daveho/DIY8bit/Episode0a/README.md

# Episode A: Arduino-based EEPROM programmer

This episode documents a project to create a programmer (hardware, firmware, host utility) for 28C64 and 28C256 EEPROM devices.

Git repo containing the schematics, firmware code, and host utility code: https://github.com/daveho/eeprog
