daveho/DIY8bit/Episode1a/Experiment02b/README.txt

Like Experiment02a, but uses 159 MHz as the main clock frequency,
meaning that the SVGA 800x600 dot clock is 39.75 MHz rather than
40 MHz. This is *almost* within the 0.5% VESA tolerance, and does
in fact work just fine on my IBM monitor.
