daveho/DIY8bit/Episode1a/Experiment02/README.txt

Experiment 2 is to connect the command FIFO to the FPGA,
without actually responding to commands sent by the host.
