daveho/DIY8bit/Episode1a/Experiment00/README.txt

Experiment 0 is just adding a reset input, but not using it.
