daveho/DIY8bit/Episode1a/Experiment01/README.txt

Experiment 1 is to add a reset input to the display
controller.
