daveho/DIY8bit/Episode05/DTypeLatchAsyncSetReset/DTypeLatchAsyncSetReset.pdf

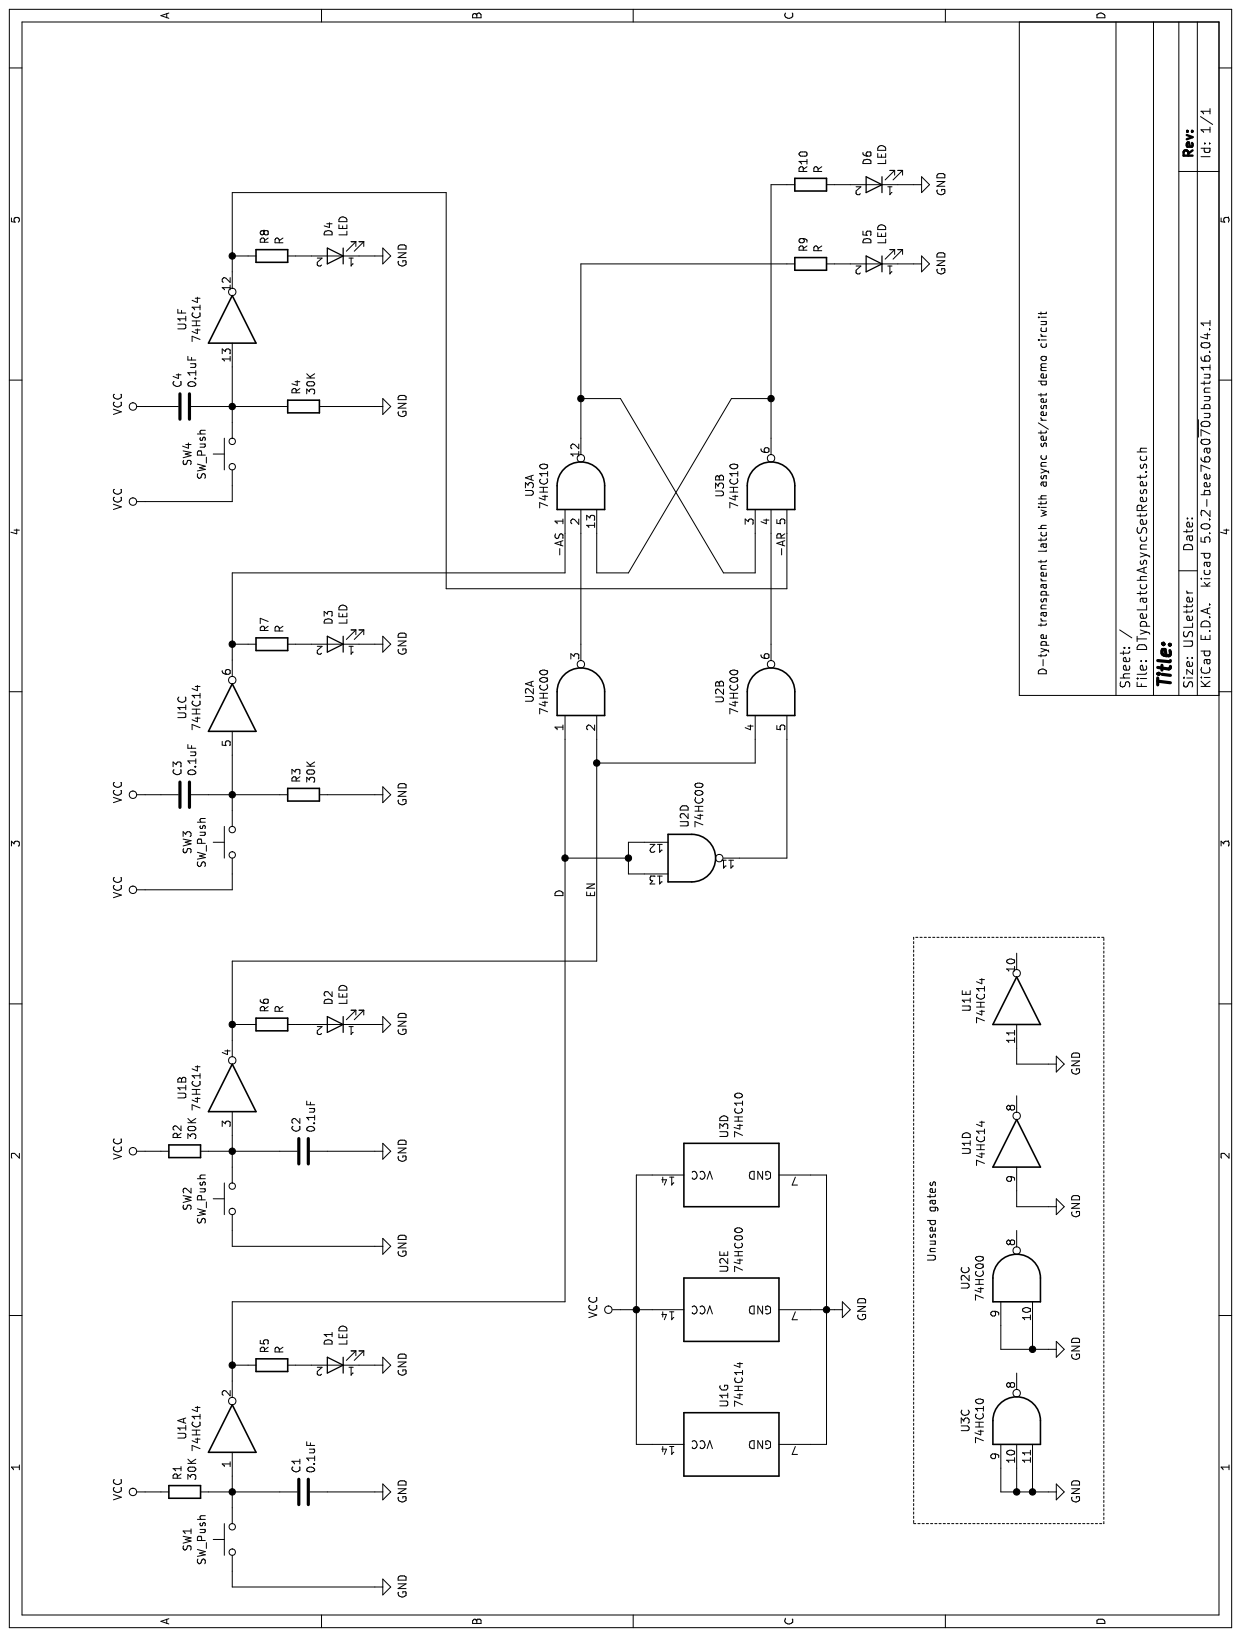
[picture p65: page 1]
