daveho/DIY8bit/Episode05/DTypeLatch/DTypeLatch.pdf

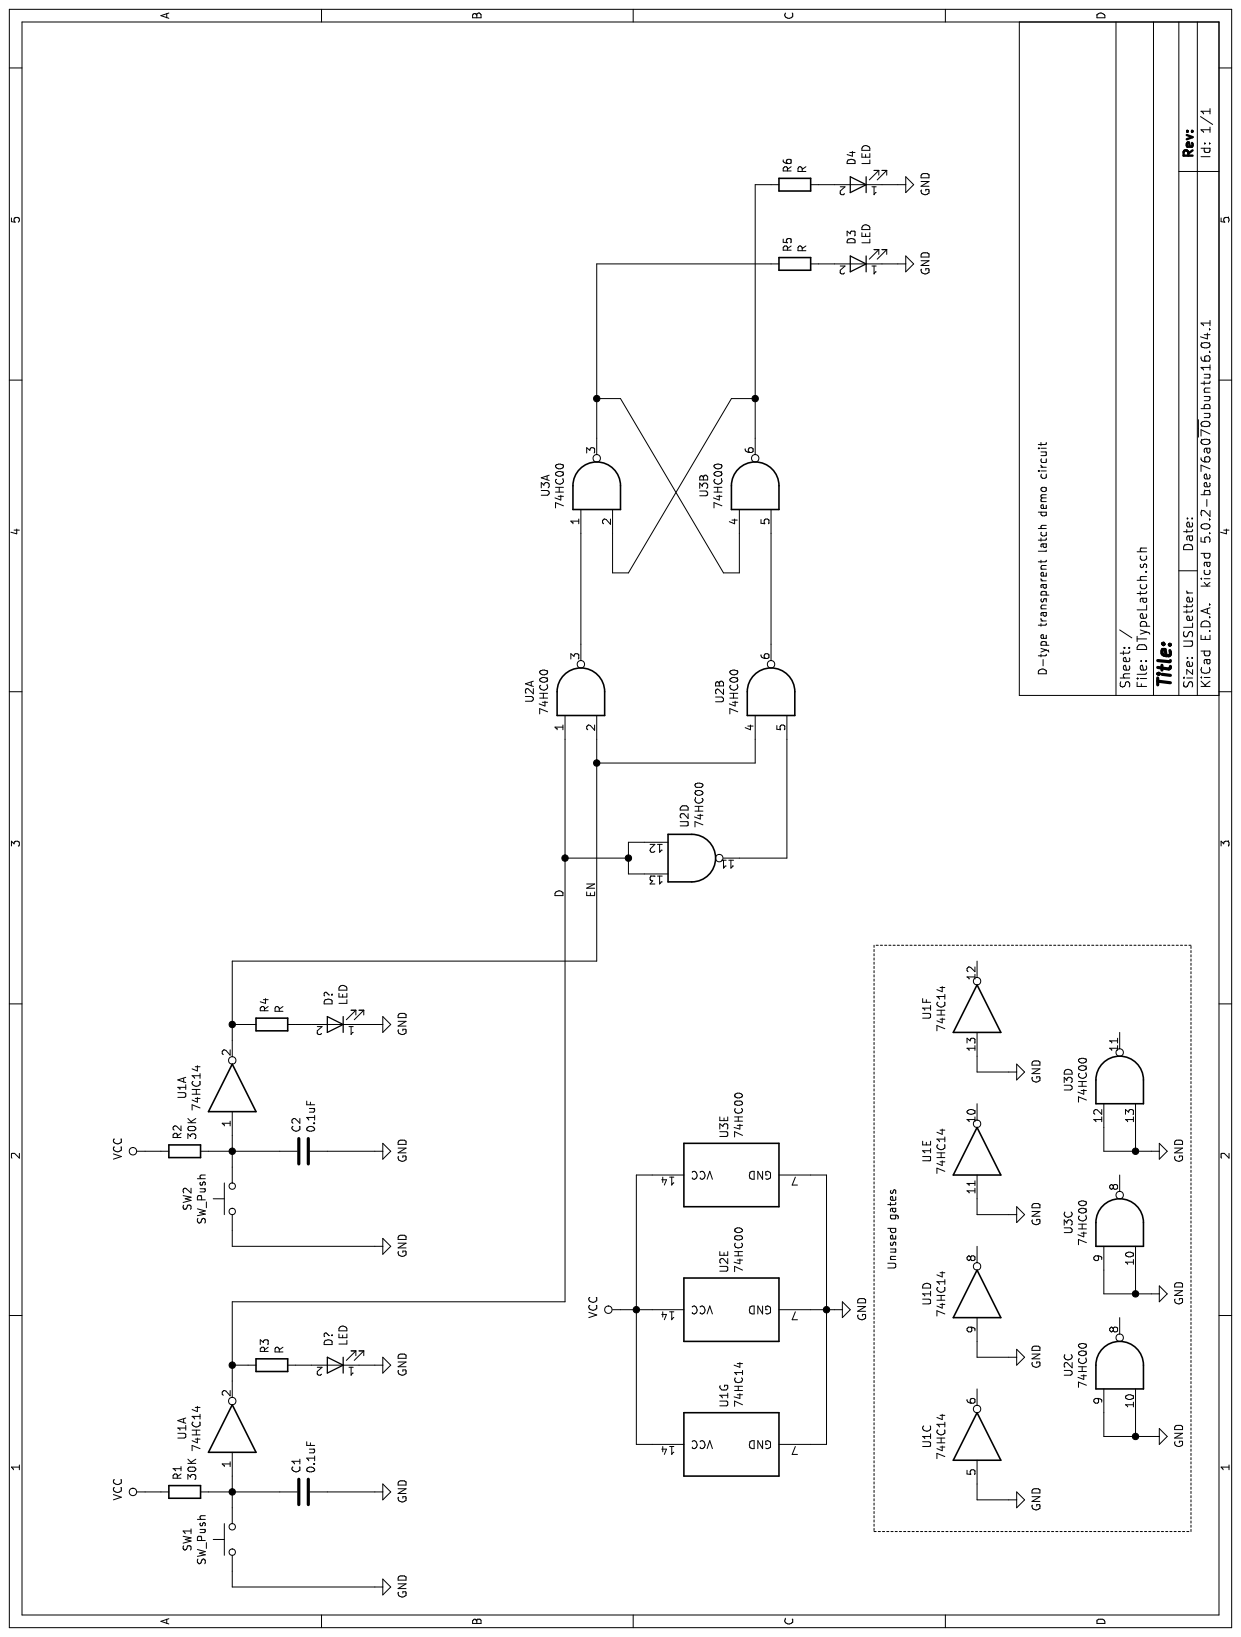
[picture p66: page 1]
