daveho/DIY8bit/Episode05/SRLatch/SRLatch.pdf

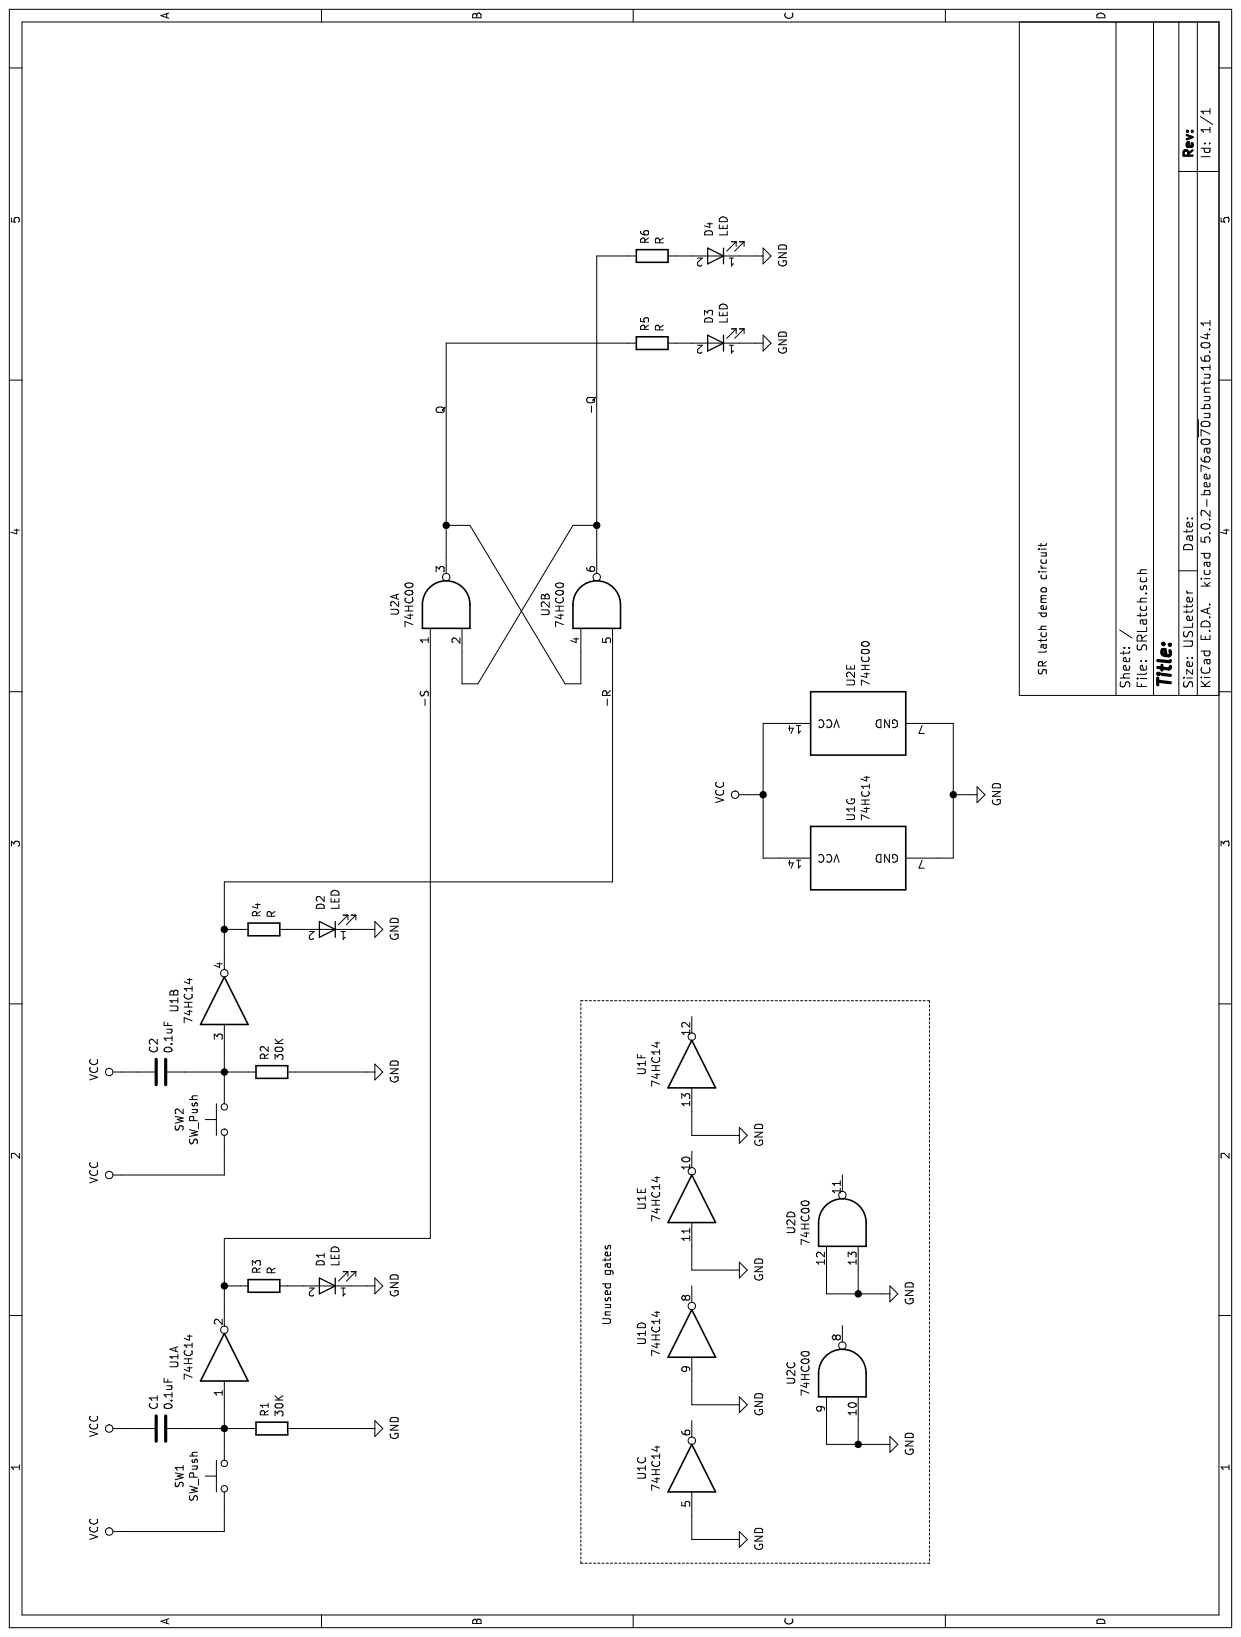
[picture p67: page 1]
