daveho/DIY8bit/Episode05/DTypeEdgeTriggered/DTypeEdgeTriggered.pdf

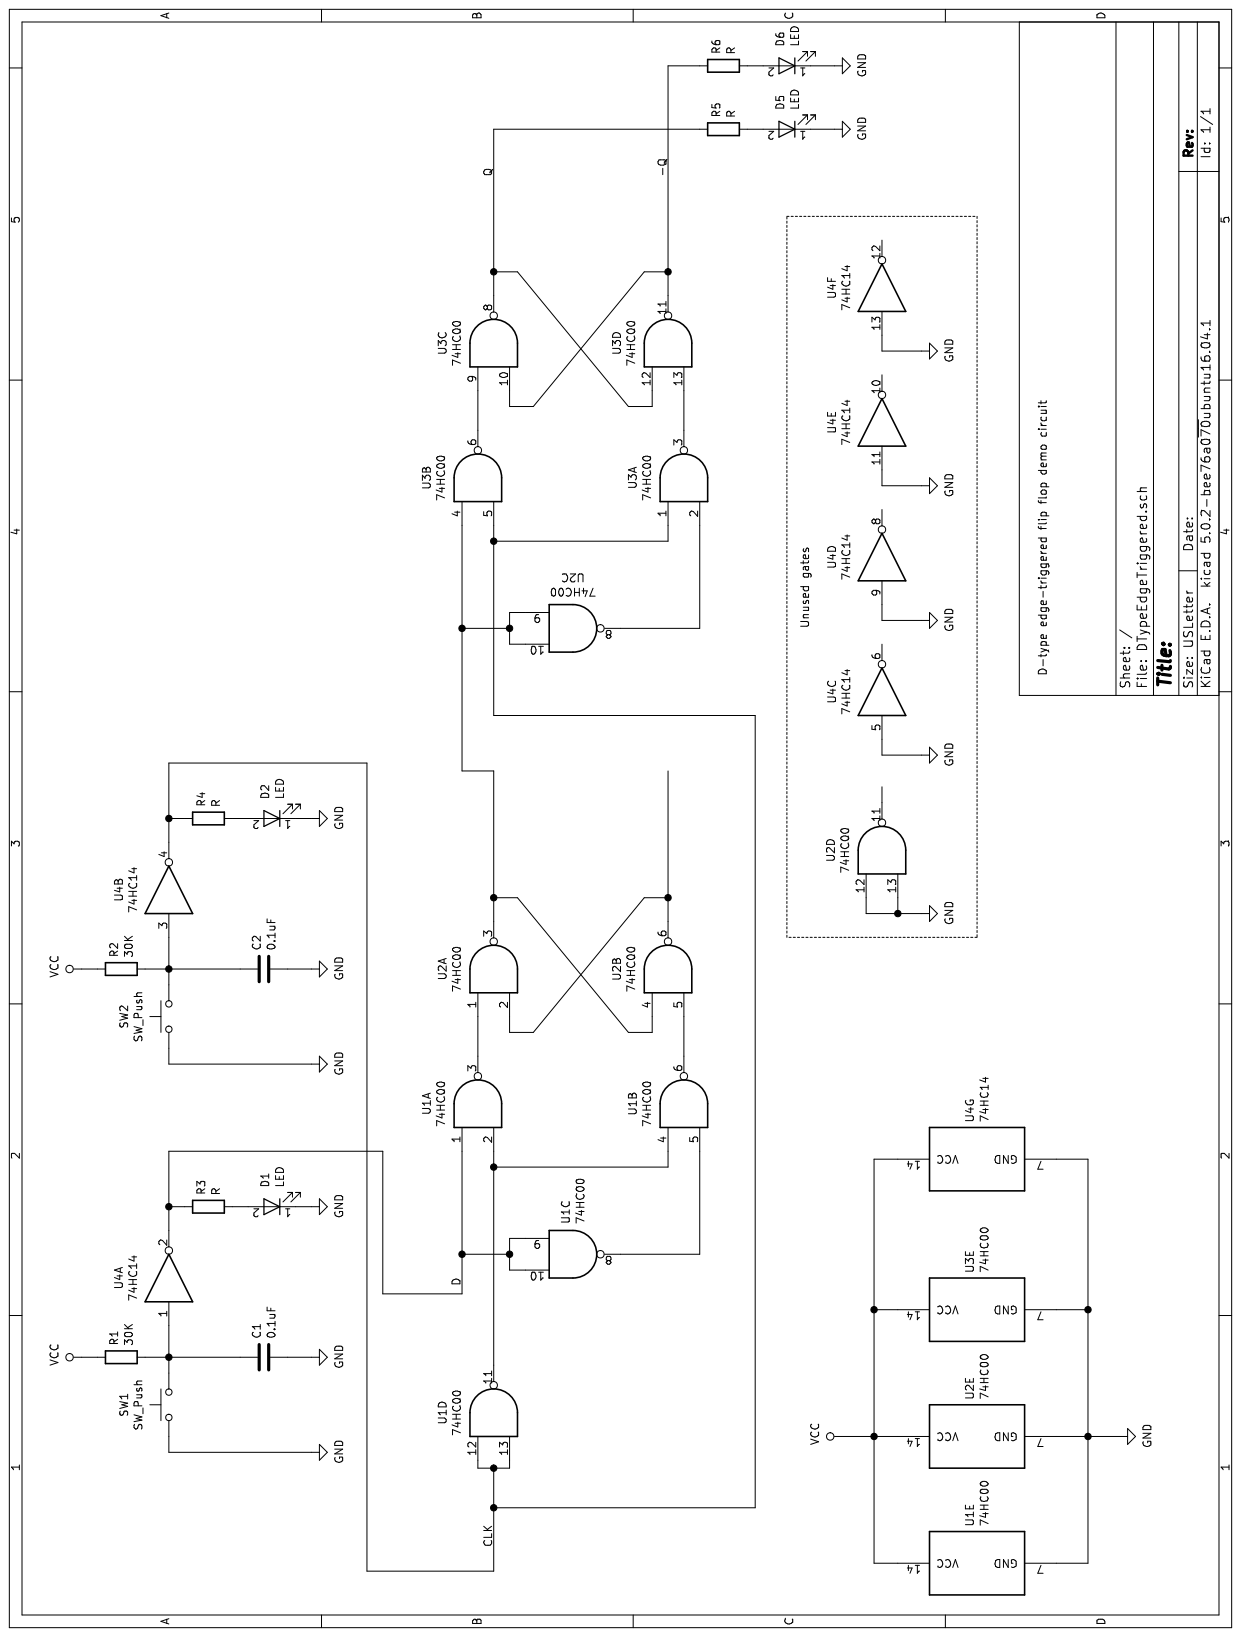
[picture p68: page 1]
