daveho/DIY8bit/GALDisplayController/HW_VGA_old.pdf

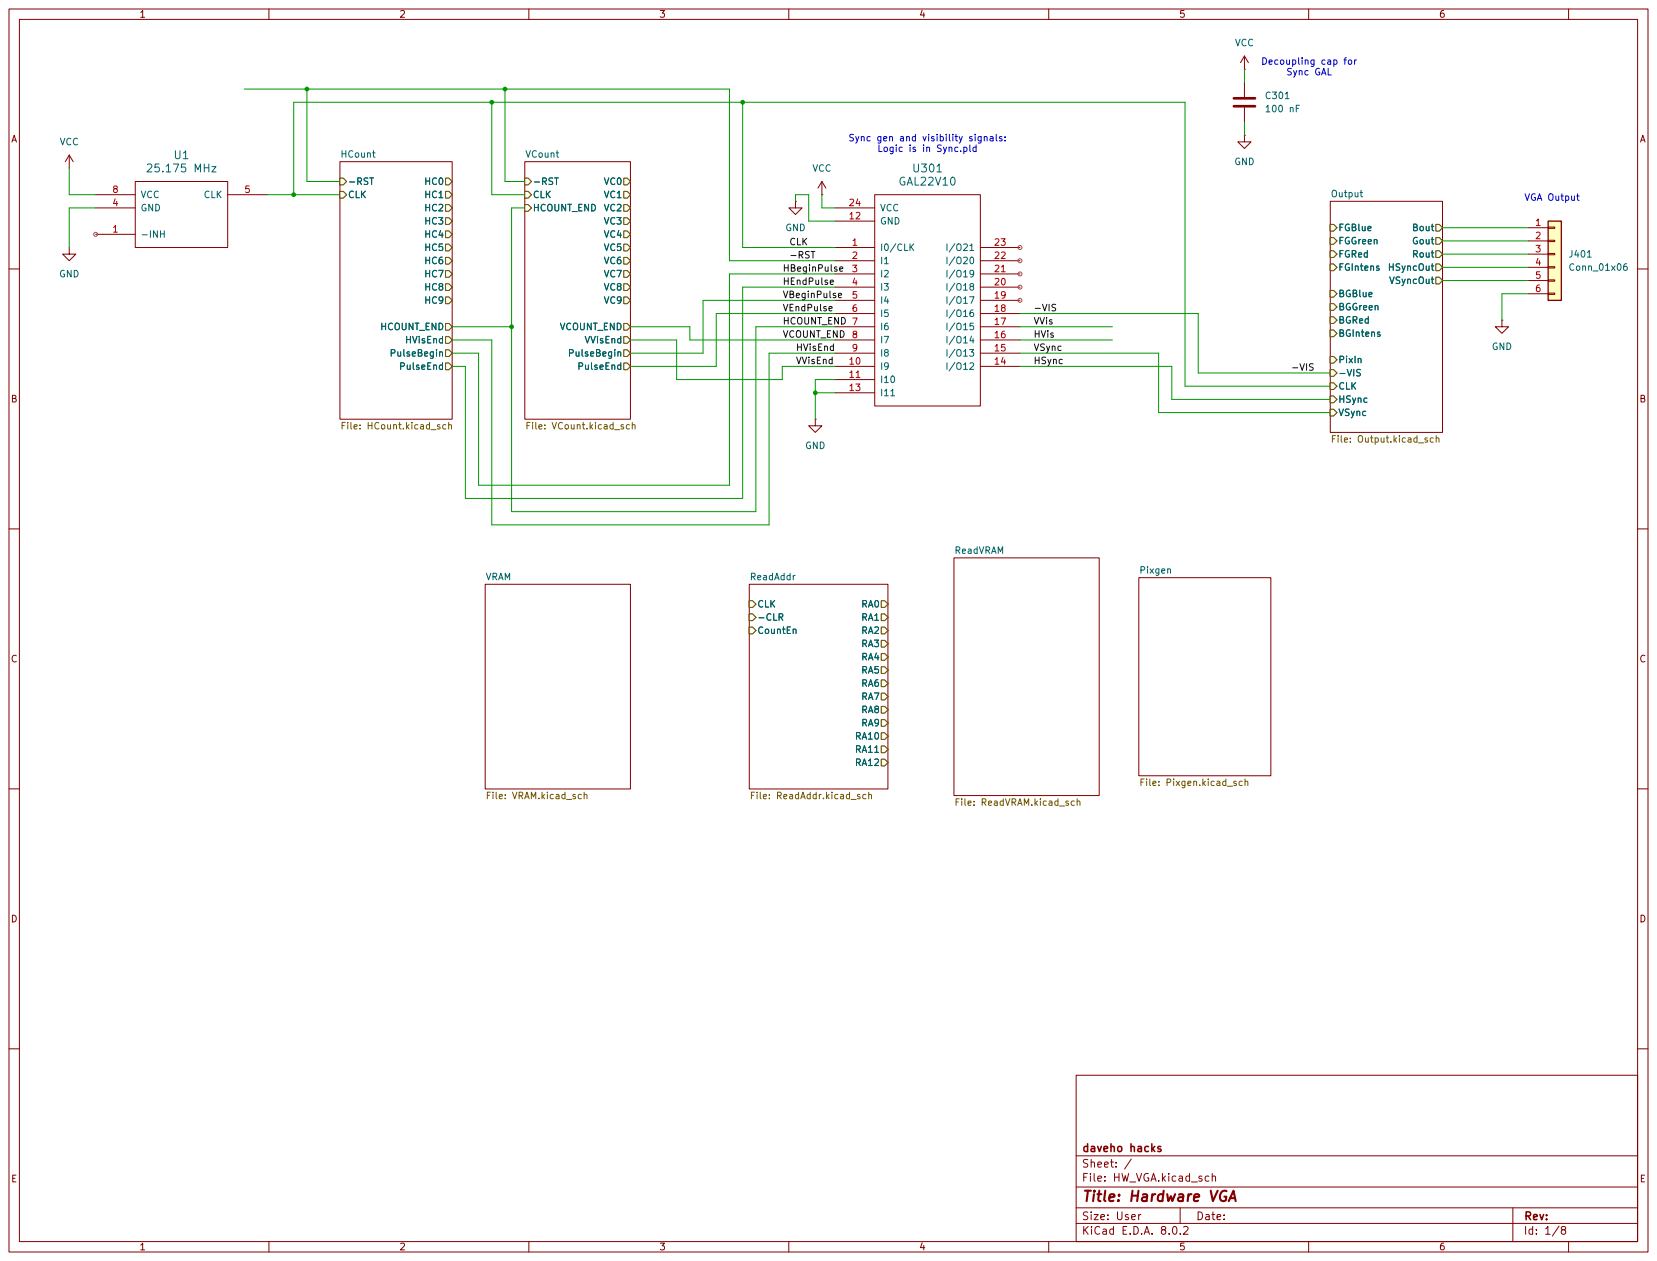
[picture p69: page 1]

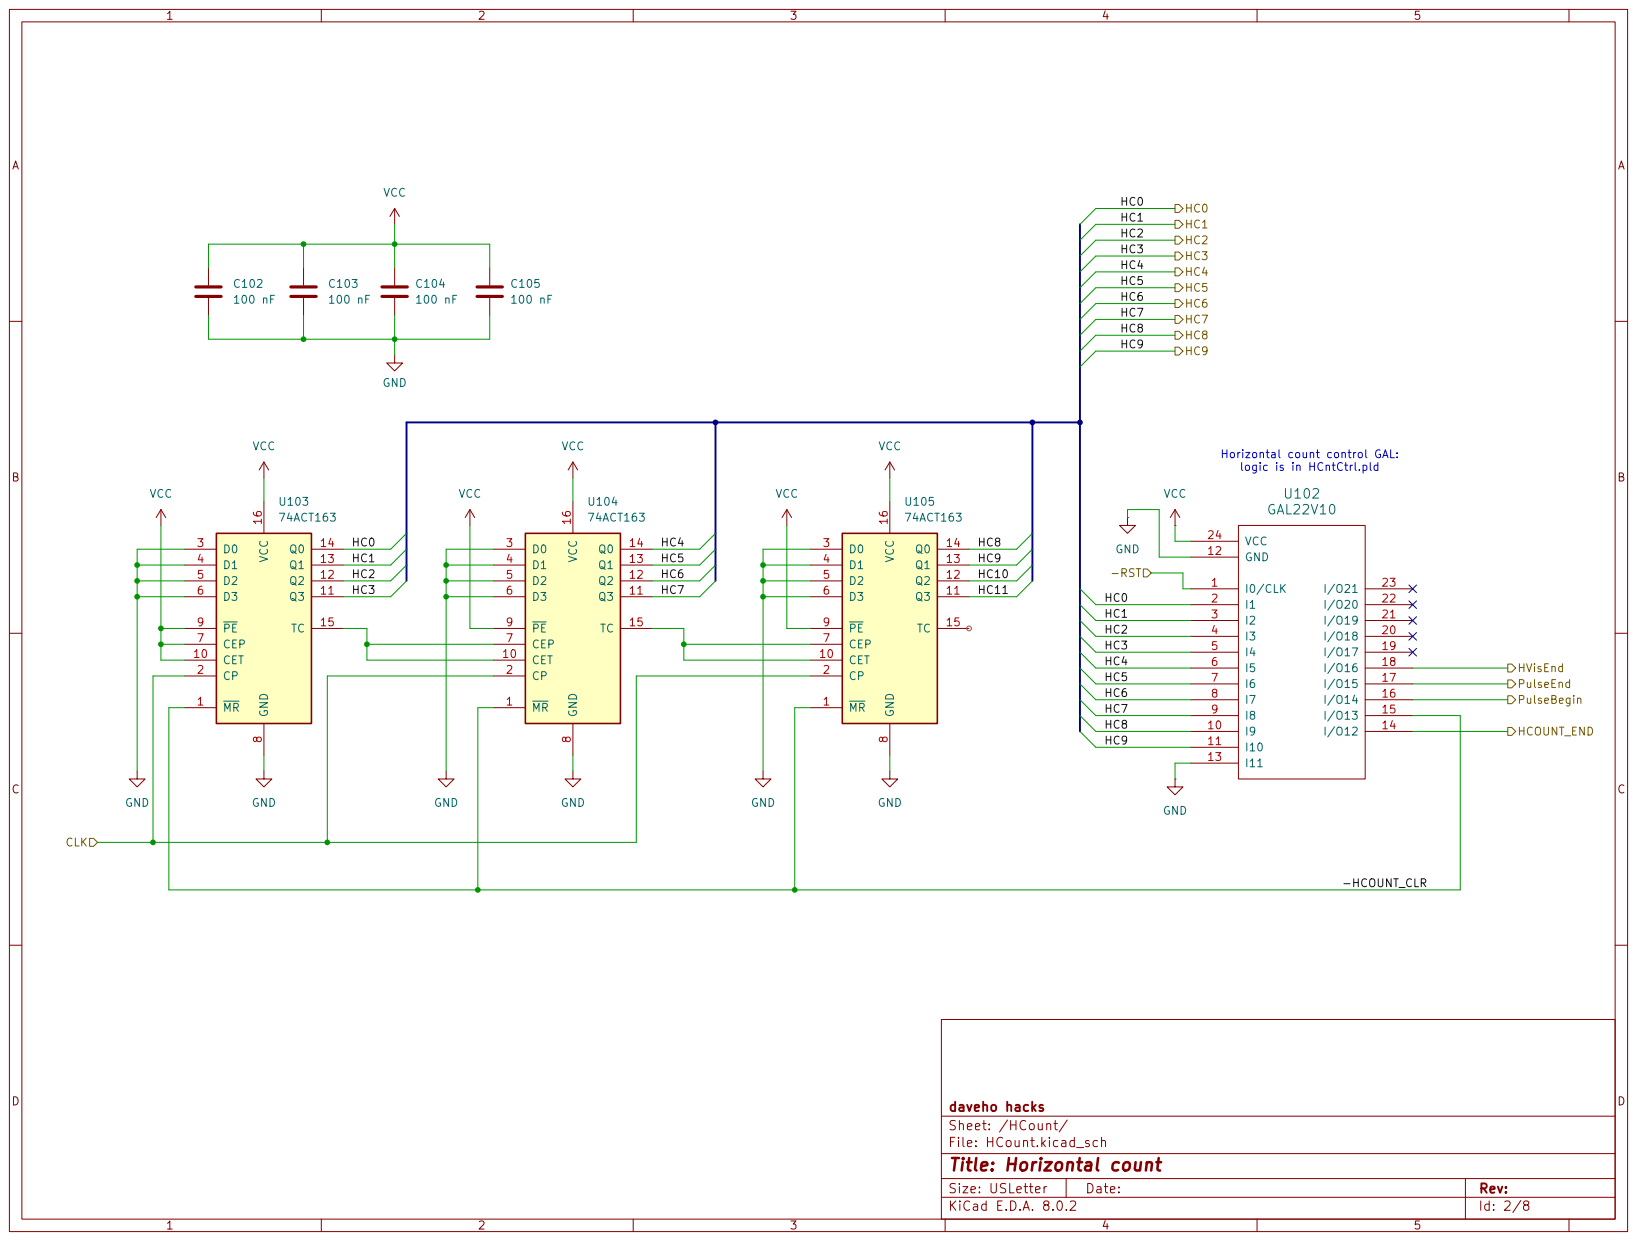
[picture p70: page 2]

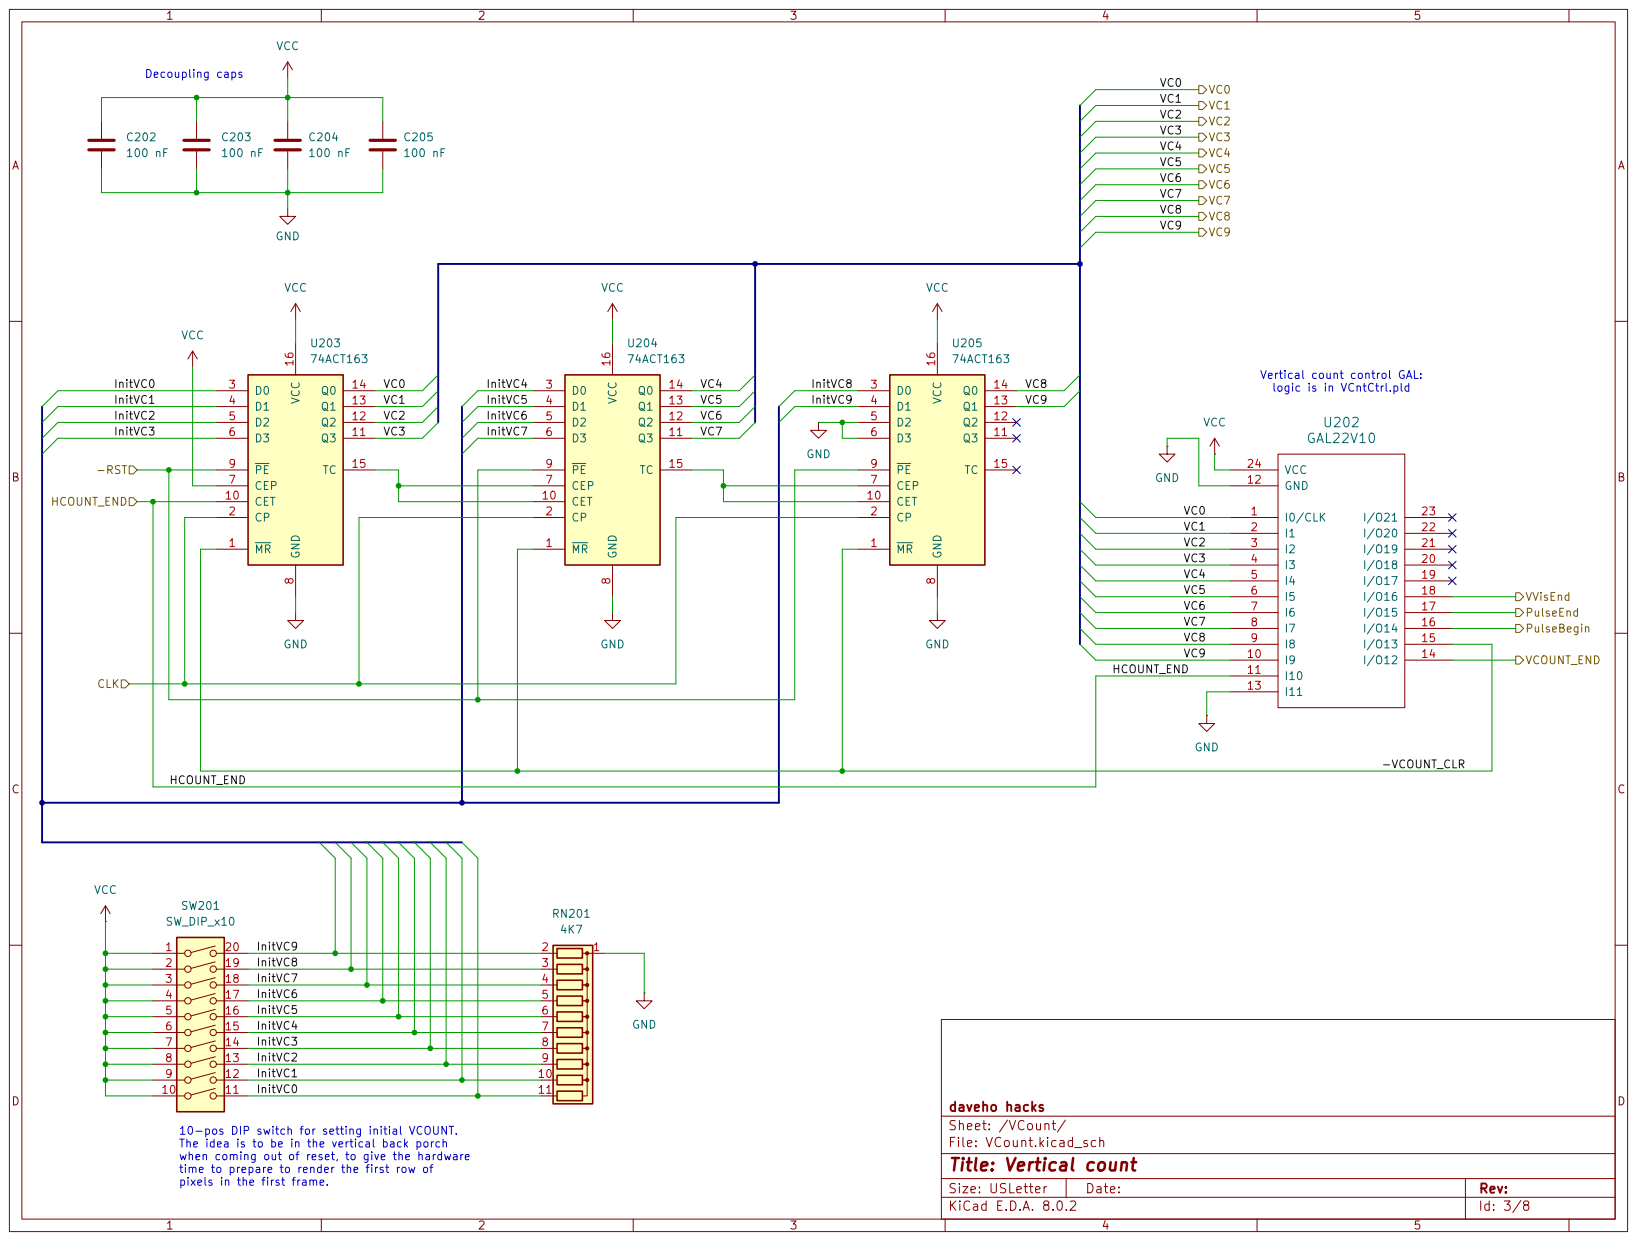
[picture p71: page 3]

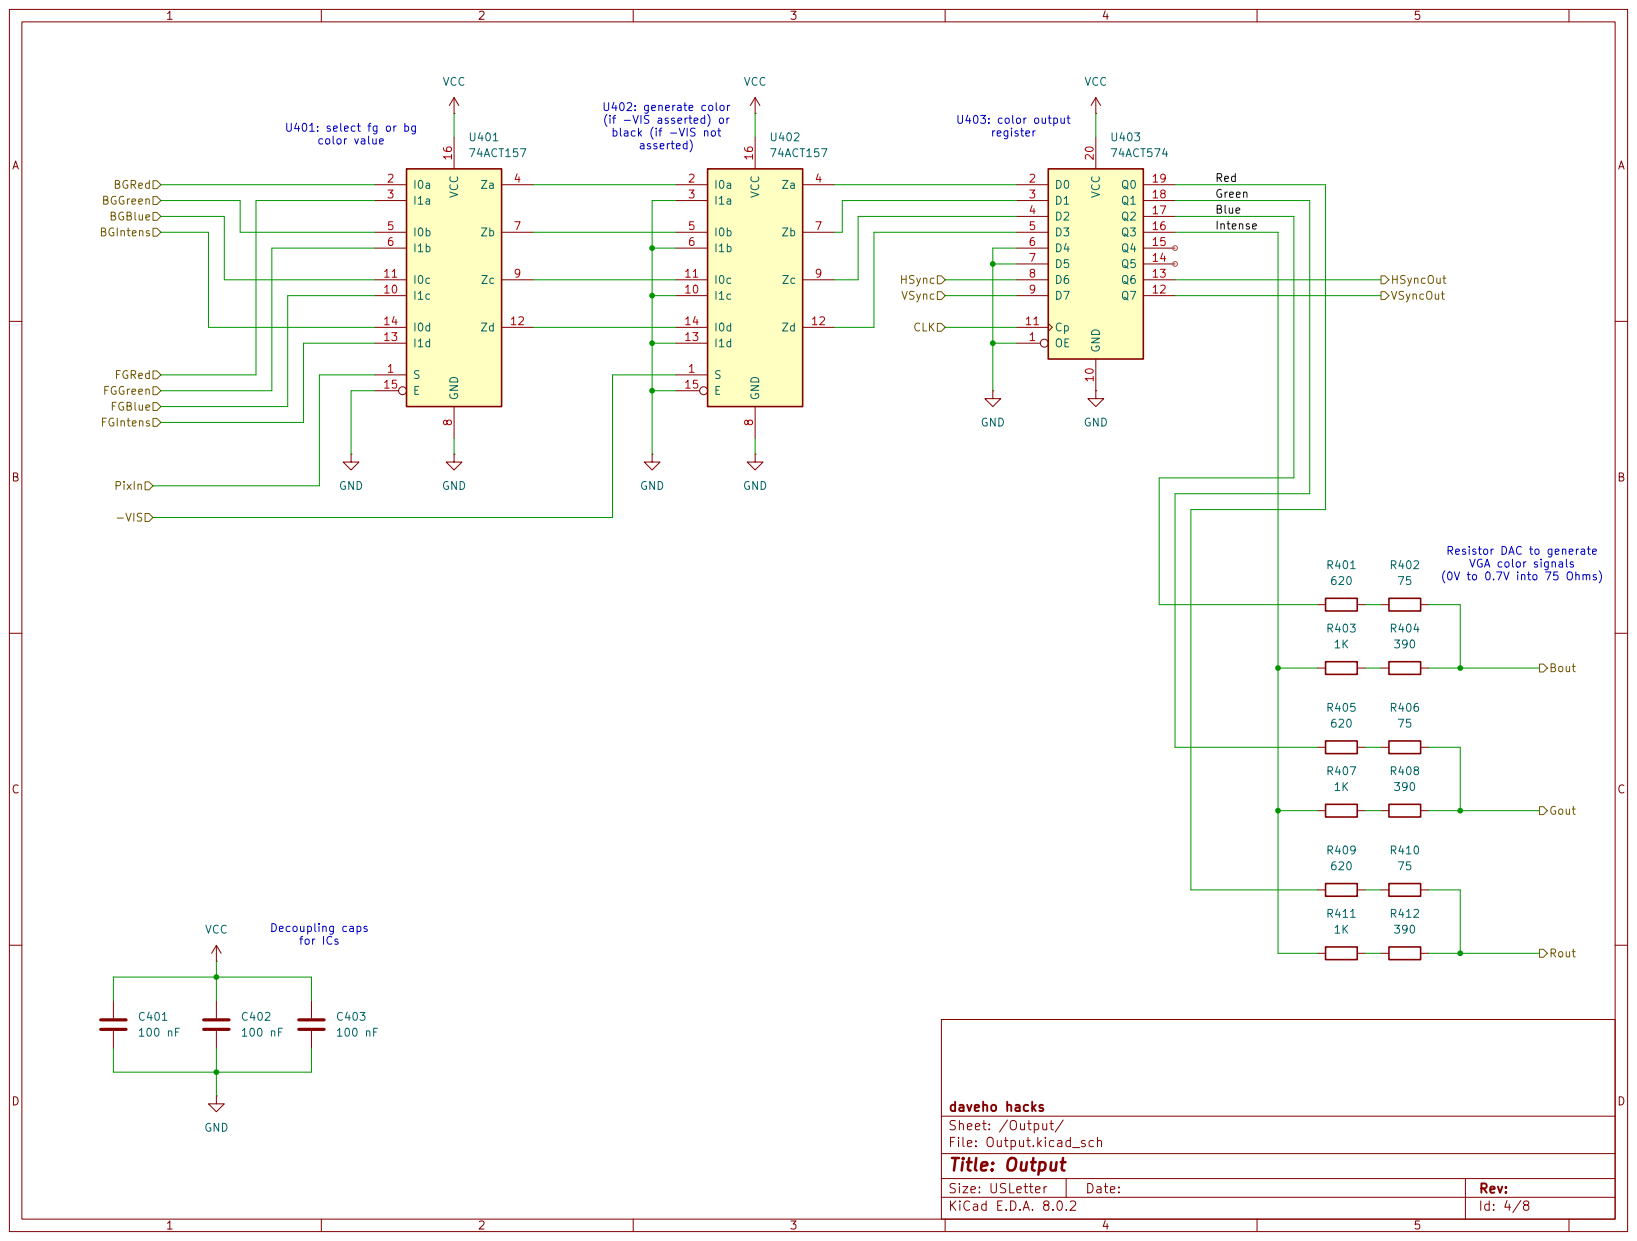
[picture p72: page 4]

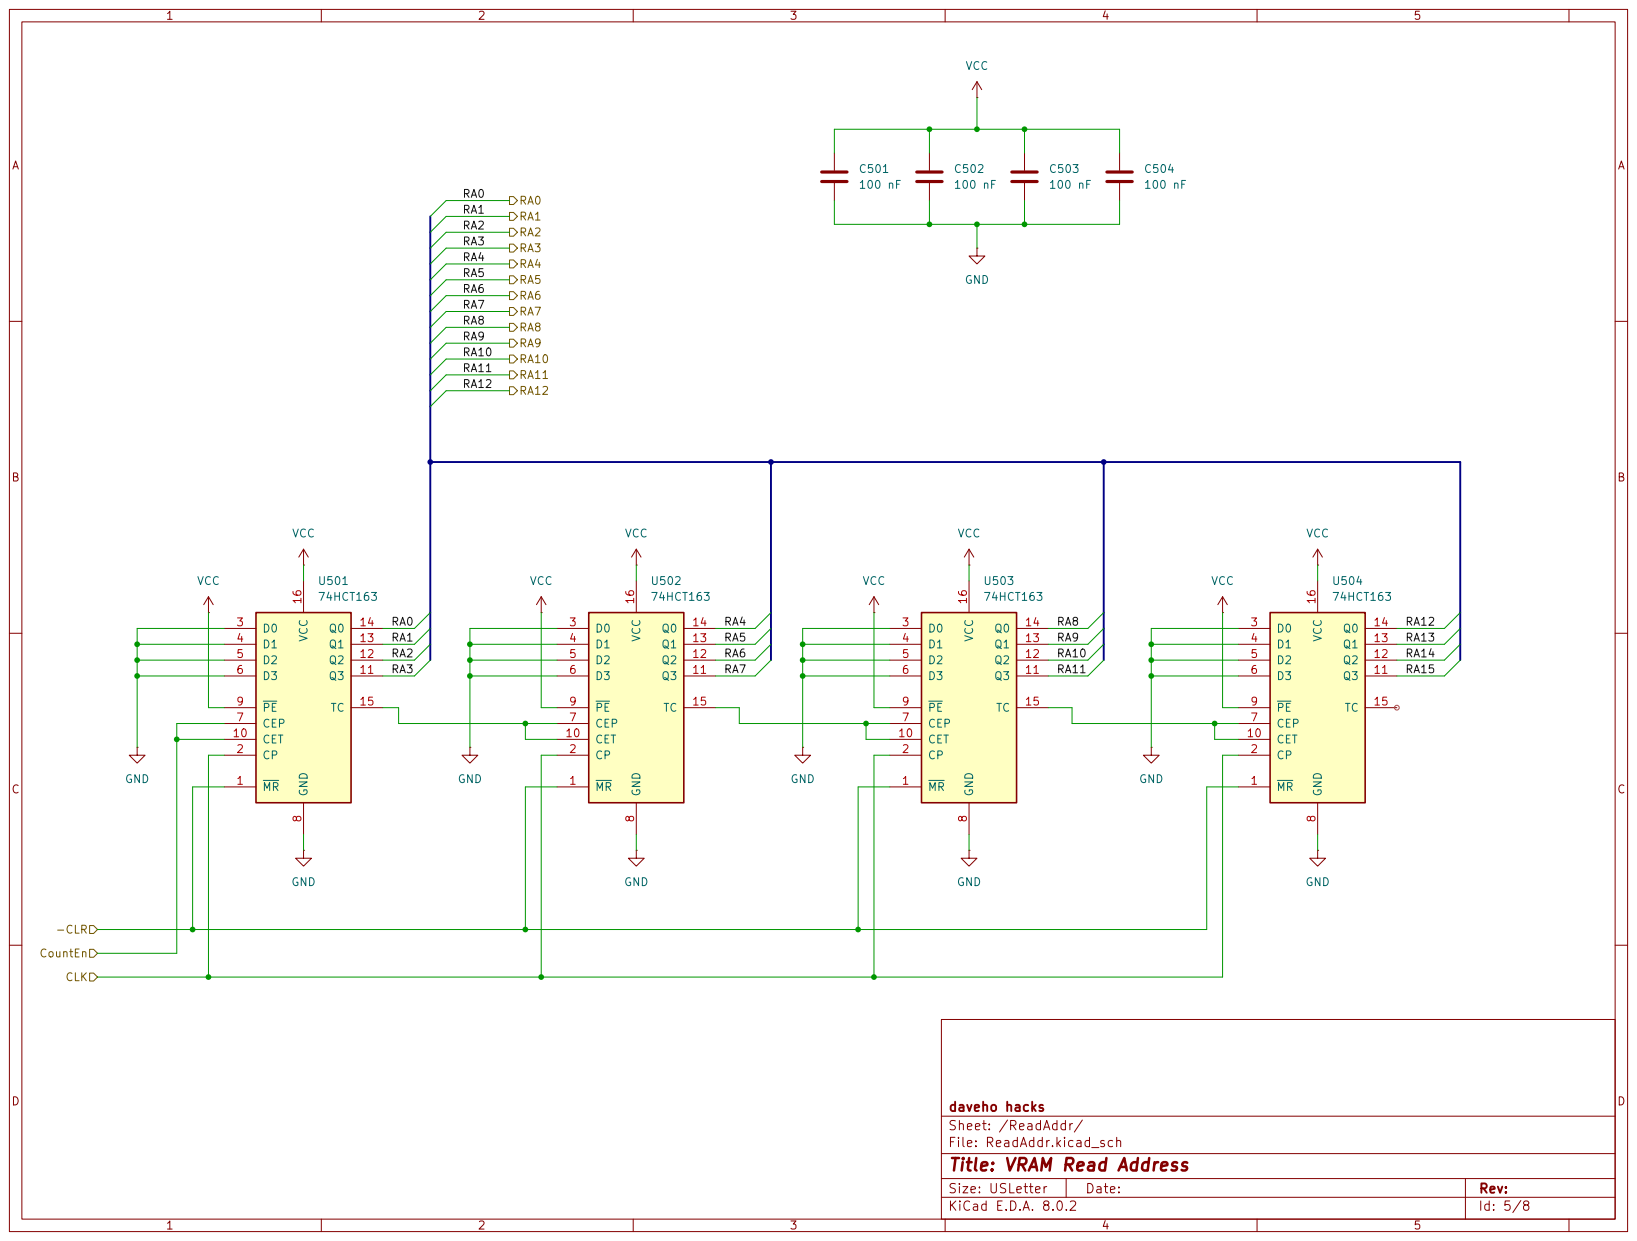
[picture p73: page 5]

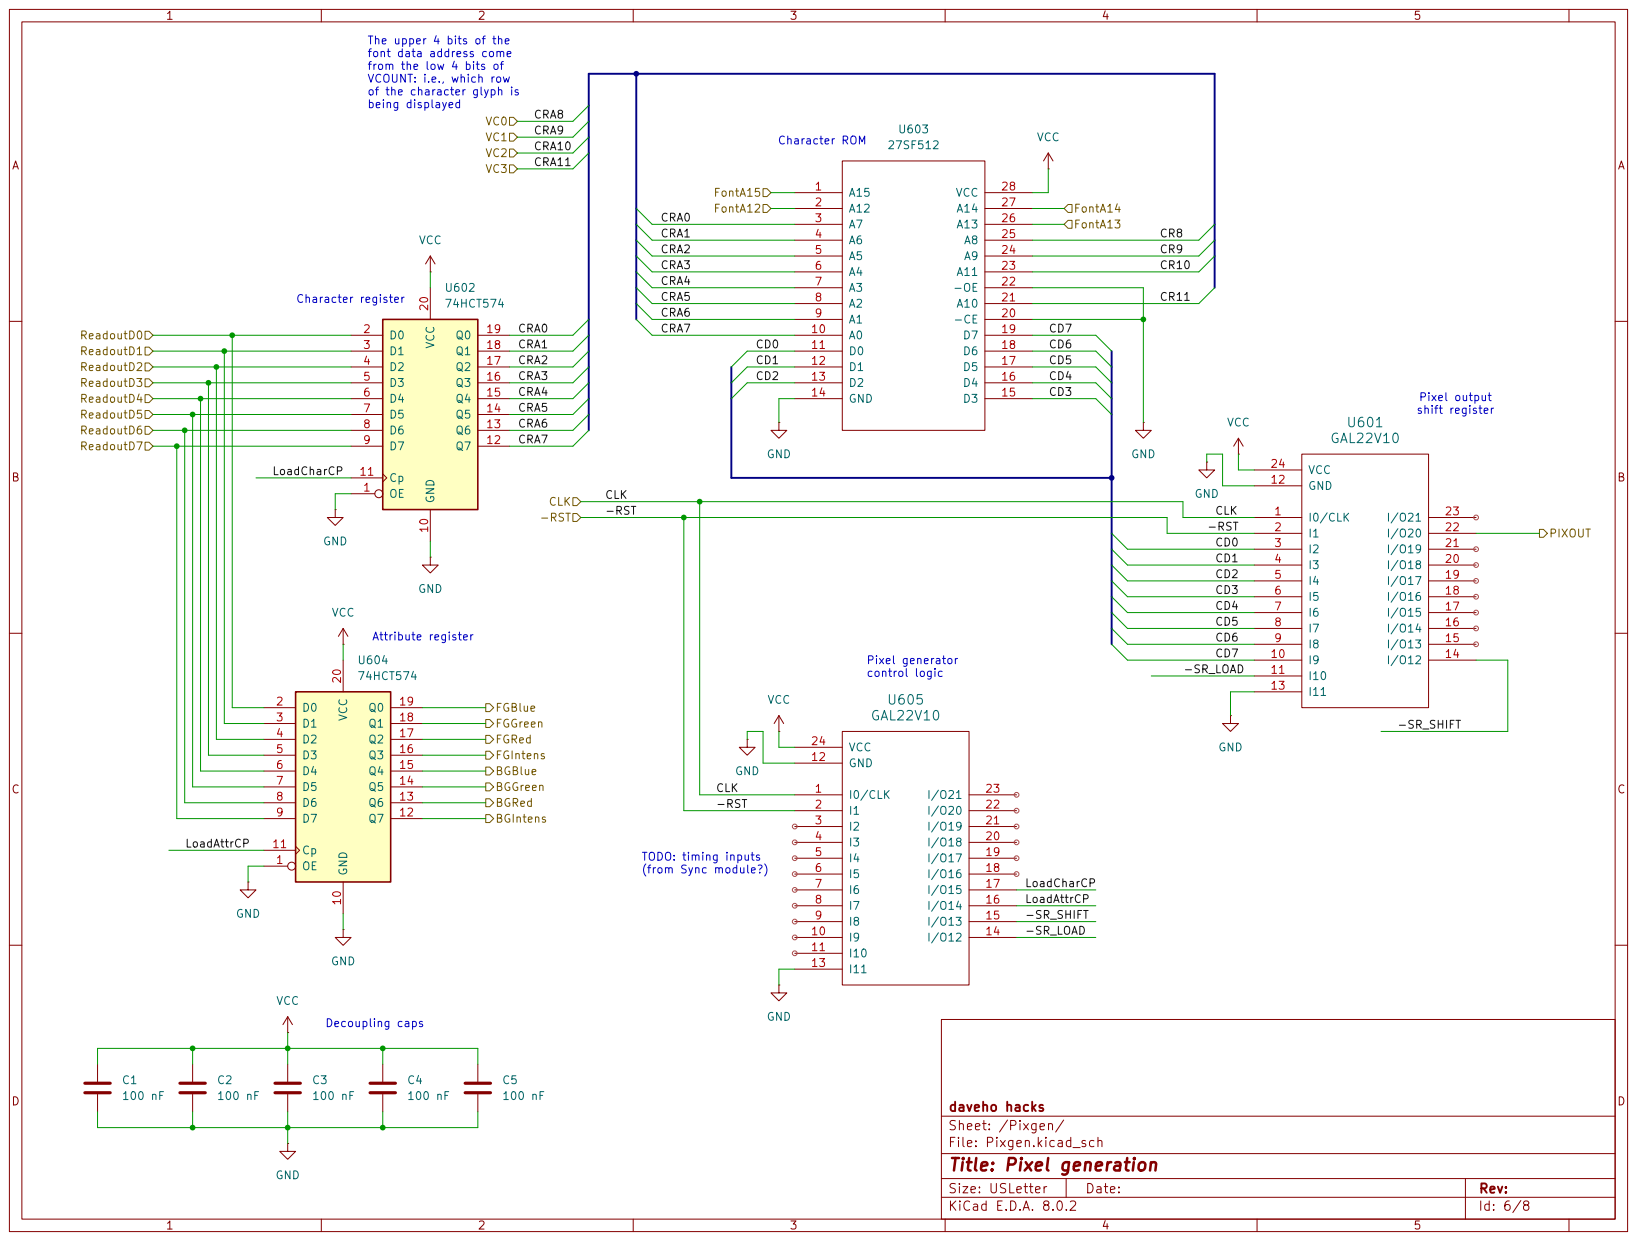
[picture p74: page 6]

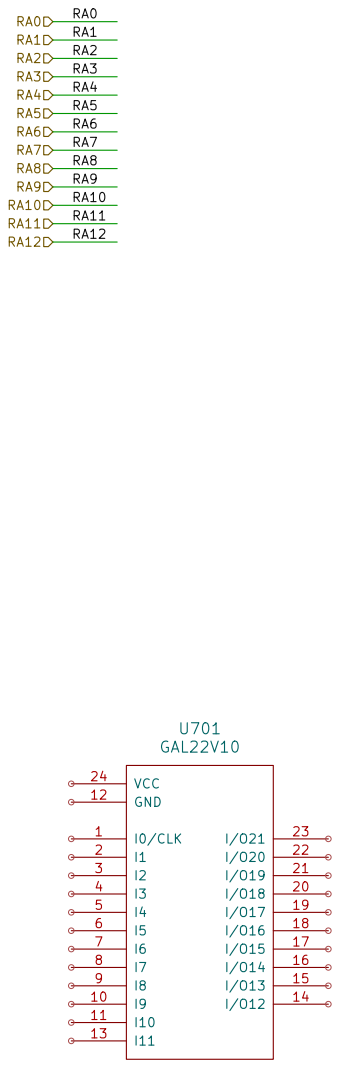
[picture p75: page 7]

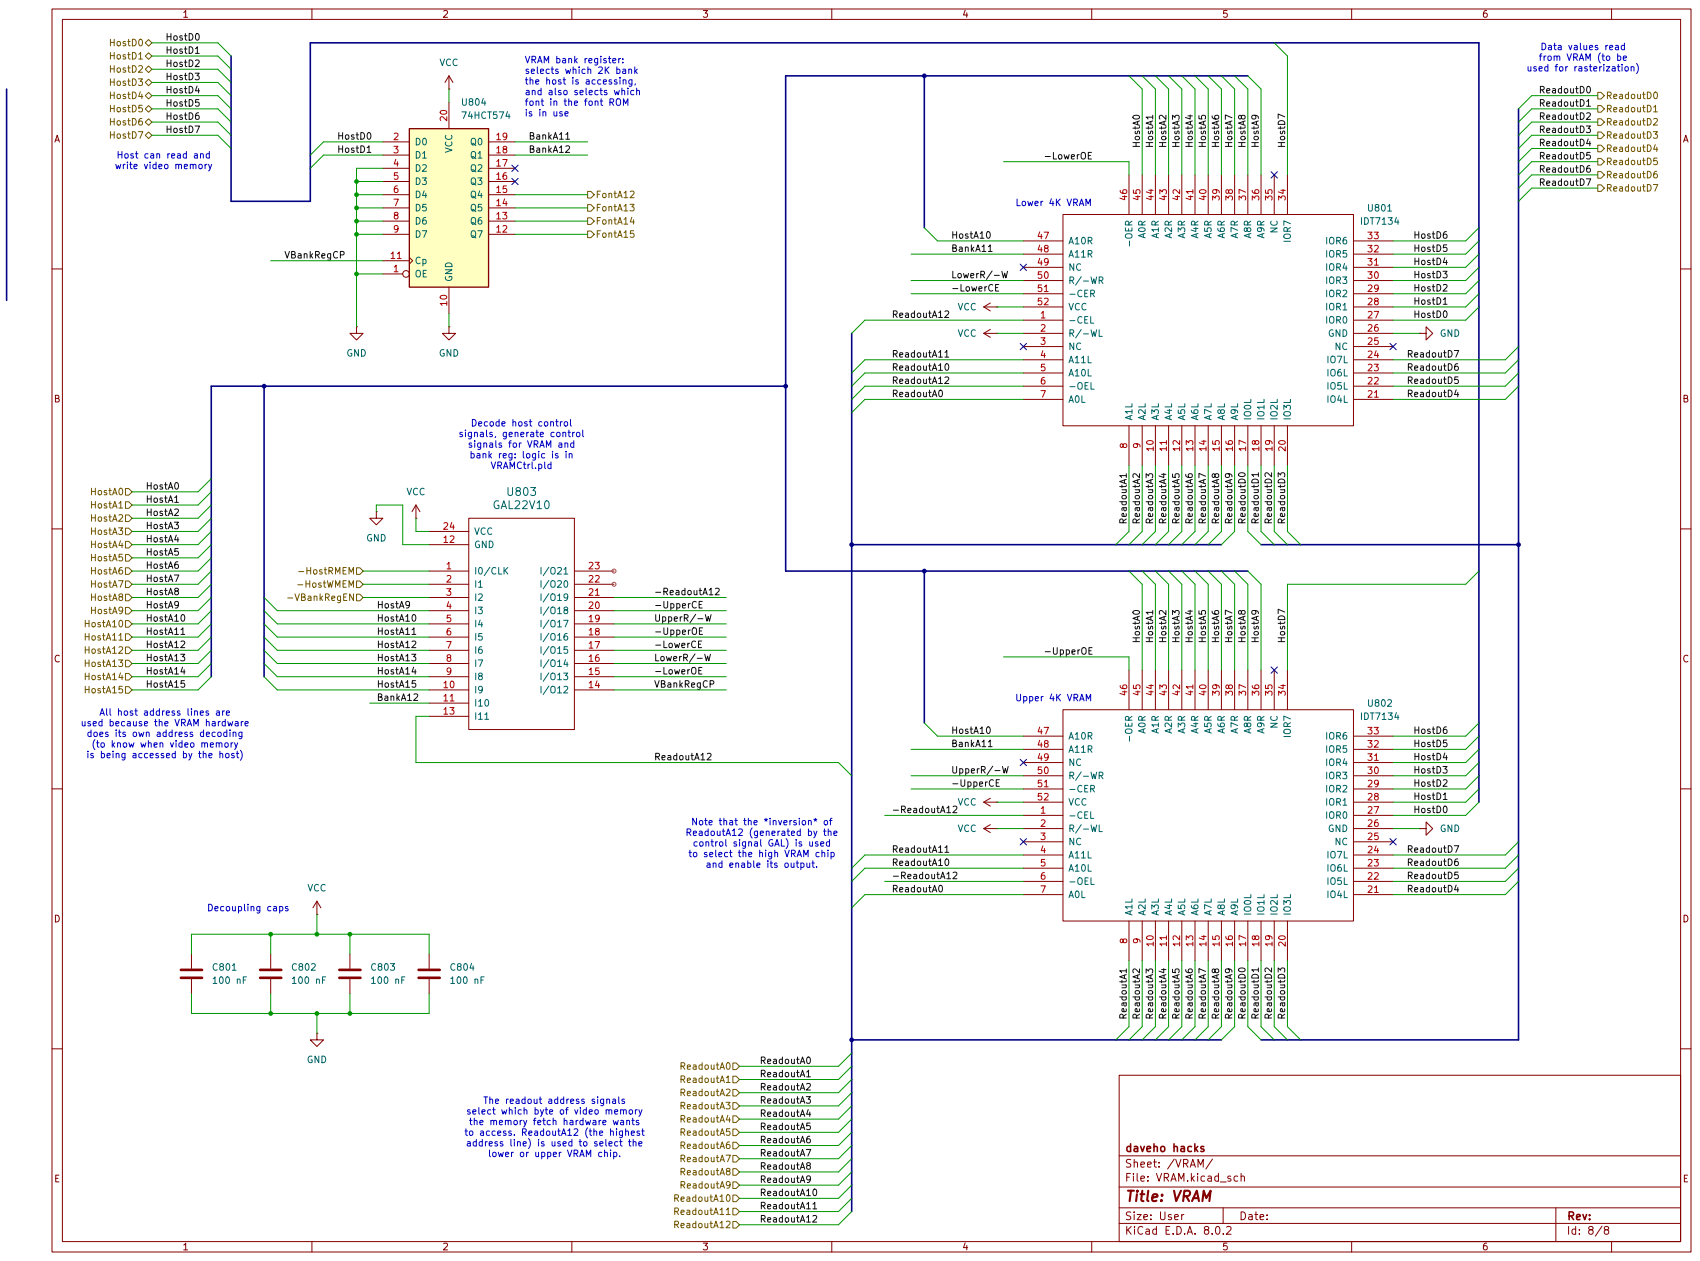
[picture p76: page 8]
