daveho/DIY8bit/HardwareDesign/TMS9918A_YM2149.kicad_pcb

## KiCad design HardwareDesign/TMS9918A_YM2149.kicad_pcb (2023-02-11)

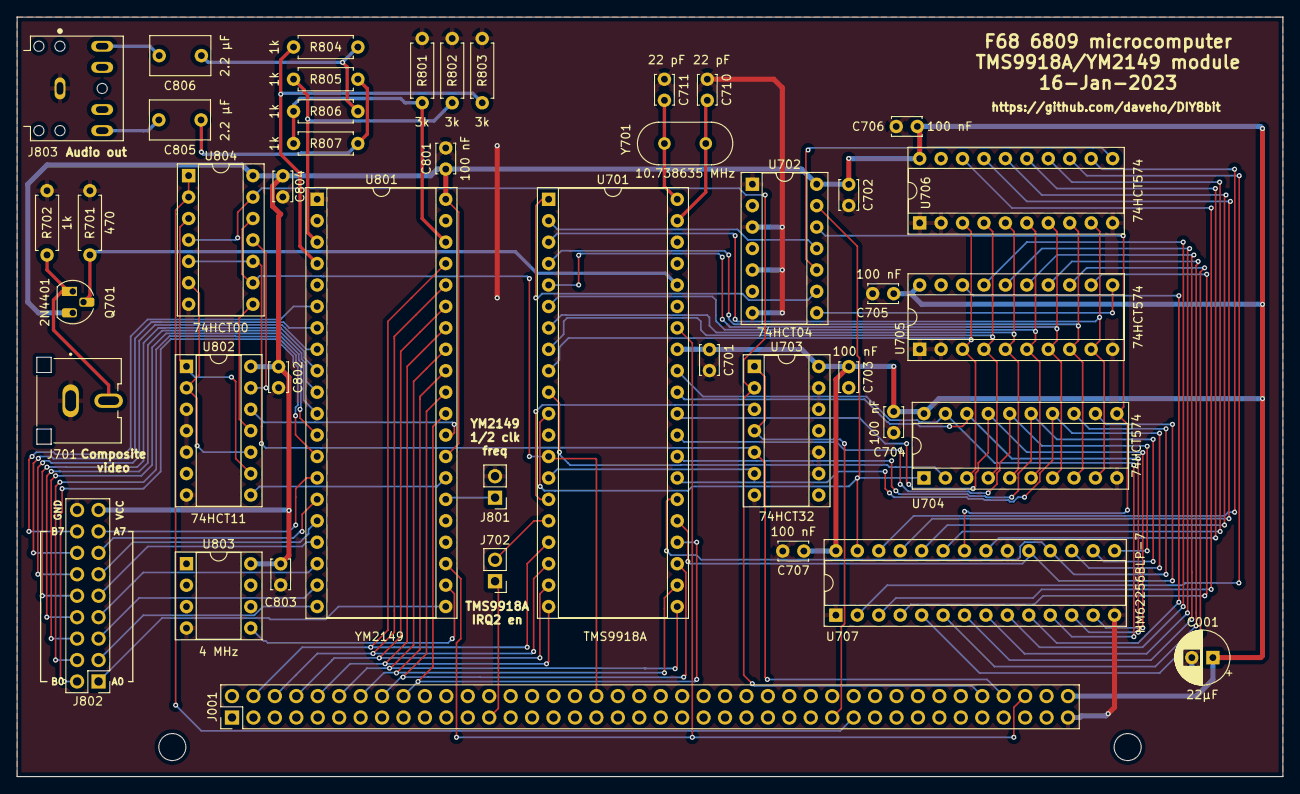
[picture p88: board TMS9918A_YM2149.kicad_pcb from above]

Board: 2 copper layers, 150.0 x 90.0 mm, 44 parts (0 on the bottom side), 91 nets.

Parts:
C001: 22μF; CP_Radial_D6.3mm_P2.50mm
C701, C702, C703, C704, C705, C706, C707, C801, C802, C803, C804: 100 nF; C_Disc_D3.4mm_W2.1mm_P2.50mm
C710, C711: 22 pF; C_Disc_D3.4mm_W2.1mm_P2.50mm
C805, C806: 2.2 μF; C_Rect_L7.0mm_W4.5mm_P5.00mm
J001: Conn_02x40_Odd_Even; PinHeader_2x40_P2.54mm_Vertical
J701: RCJ-044; CUI_RCJ-044
J702, J801: Conn_01x02; PinHeader_1x02_P2.54mm_Vertical
J802: Conn_02x09_Odd_Even; PinHeader_2x09_P2.54mm_Vertical
J803: SJ1-3525N; CUI_SJ1-3525N
Q701: 2N4401; TO-92_HandSolder
R701: 470; R_Axial_DIN0207_L6.3mm_D2.5mm_P7.62mm_Horizontal
R702, R804, R805, R806, R807: 1k; R_Axial_DIN0207_L6.3mm_D2.5mm_P7.62mm_Horizontal
R801, R802, R803: 3k; R_Axial_DIN0207_L6.3mm_D2.5mm_P7.62mm_Horizontal
U701: TMS9918A; DIP-40_W15.24mm_Socket
U702: 74HCT04; DIP-14_W7.62mm_Socket
U703: 74HCT32; DIP-14_W7.62mm_Socket
U704, U705, U706: 74HCT574; DIP-20_W7.62mm_Socket
U707: HM62256BLP-7; DIP-28_W7.62mm_Socket
U801: YM2149; DIP-40_W15.24mm_Socket
U802: 74HCT11; DIP-14_W7.62mm_Socket
U803: 4 MHz; DIP-8_W7.62mm_Socket
U804: 74HCT00; DIP-14_W7.62mm_Socket
Y701: 10.738635 MHz; Crystal_HC18-U_Vertical

Connections:
/A0: J001.36, U701.13 (MODE), U804.9, U804.12
/D0: J001.4, U701.17 (CD7), U801.37 (DA0)
/D1: J001.6, U701.18 (CD6), U801.36 (DA1)
/D2: J001.8, U701.19 (CD5), U801.35 (DA2)
/D3: J001.10, U701.20 (CD4), U801.34 (DA3)
/D4: J001.12, U701.21 (CD3), U801.33 (DA4)
/D5: J001.14, U701.22 (CD2), U801.32 (DA5)
/D6: J001.16, U701.23 (CD1), U801.31 (DA6)
/D7: J001.18, U701.24 (CD0), U801.30 (DA7)
/TMS9918ADisplay/AD0: U701.10 (AD0), U704.2 (D0)
/TMS9918ADisplay/AD1: U701.9 (AD1), U704.3 (D1), U705.3 (D1), U706.3 (D1)
/TMS9918ADisplay/AD2: U701.8 (AD2), U704.4 (D2), U705.4 (D2), U706.4 (D2)
/TMS9918ADisplay/AD3: U701.7 (AD3), U704.5 (D3), U705.5 (D3), U706.5 (D3)
/TMS9918ADisplay/AD4: U701.6 (AD4), U704.6 (D4), U705.6 (D4), U706.6 (D4)
/TMS9918ADisplay/AD5: U701.5 (AD5), U704.7 (D5), U705.7 (D5), U706.7 (D5)
/TMS9918ADisplay/AD6: U701.4 (AD6), U704.8 (D6), U705.8 (D6), U706.8 (D6)
/TMS9918ADisplay/AD7: U701.3 (AD7), U704.9 (D7), U705.9 (D7), U706.9 (D7)
/TMS9918ADisplay/VA0: U705.18 (Q1), U707.10 (A0)
/TMS9918ADisplay/VA1: U705.17 (Q2), U707.9 (A1)
/TMS9918ADisplay/VA2: U705.16 (Q3), U707.8 (A2)
/TMS9918ADisplay/VA3: U705.15 (Q4), U707.7 (A3)
/TMS9918ADisplay/VA4: U705.14 (Q5), U707.6 (A4)
/TMS9918ADisplay/VA5: U705.13 (Q6), U707.5 (A5)
/TMS9918ADisplay/VA6: U705.12 (Q7), U707.4 (A6)
/TMS9918ADisplay/VA7: U706.18 (Q1), U707.3 (A7)
/TMS9918ADisplay/VA8: U706.17 (Q2), U707.25 (A8)
/TMS9918ADisplay/VA9: U706.16 (Q3), U707.24 (A9)
/TMS9918ADisplay/VA10: U706.15 (Q4), U707.21 (A10)
/TMS9918ADisplay/VA11: U706.14 (Q5), U707.23 (A11)
/TMS9918ADisplay/VA12: U706.13 (Q6), U707.2 (A12)
/TMS9918ADisplay/VA13: U706.12 (Q7), U707.26 (A13)
/TMS9918ADisplay/VD0: U701.32 (RD0), U704.19 (Q0), U707.11 (D0)
/TMS9918ADisplay/VD1: U701.31 (RD1), U704.18 (Q1), U707.12 (D1)
/TMS9918ADisplay/VD2: U701.30 (RD2), U704.17 (Q2), U707.13 (D2)
/TMS9918ADisplay/VD3: U701.29 (RD3), U704.16 (Q3), U707.15 (D3)
/TMS9918ADisplay/VD4: U701.28 (RD4), U704.15 (Q4), U707.16 (D4)
/TMS9918ADisplay/VD5: U701.27 (RD5), U704.14 (Q5), U707.17 (D5)
/TMS9918ADisplay/VD6: U701.26 (RD6), U704.13 (Q6), U707.18 (D6)
/TMS9918ADisplay/VD7: U701.25 (RD7), U704.12 (Q7), U707.19 (D7)
/TMS9918ADisplay/VR/~W: U701.11 (R/~W), U702.13, U704.1 (OE), U707.27 (~WE)
/TMS9918ADisplay/V~R/W: U702.12, U704.11 (Cp), U707.22 (~OE)
/TMS9918ADisplay/~CAS: U701.2 (~CAS), U702.11
/TMS9918ADisplay/~RAS: U701.1 (~RAS), U702.9
/TMS9918ADisplay/~VDPRD: U701.15 (~CSR), U703.3
/TMS9918ADisplay/~VDPWR: U701.14 (~CSW), U703.6
/YM2149_Sound/ANLG_A: R803.1, R804.1, U801.4 (ANLG_A)
/YM2149_Sound/ANLG_B: R802.1, R805.1, U801.3 (ANLG_B)
/YM2149_Sound/ANLG_C: R801.1, R806.1, R807.1, U801.38 (ANLG_C)
/YM2149_Sound/BC1: U801.29 (BC1), U802.12
/YM2149_Sound/BDIR: U801.27 (BDIR), U802.8
/YM2149_Sound/IOA0: J802.1, U801.21 (IOA0)
/YM2149_Sound/IOA1: J802.3, U801.20 (IOA1)
/YM2149_Sound/IOA2: J802.5, U801.19 (IOA2)
/YM2149_Sound/IOA3: J802.7, U801.18 (IOA3)
/YM2149_Sound/IOA4: J802.9, U801.17 (IOA4)
/YM2149_Sound/IOA5: J802.11, U801.16 (IOA5)
/YM2149_Sound/IOA6: J802.13, U801.15 (IOA6)
/YM2149_Sound/IOA7: J802.15, U801.14 (IOA7)
/YM2149_Sound/IOB0: J802.2, U801.13 (IOB0)
/YM2149_Sound/IOB1: J802.4, U801.12 (IOB1)
/YM2149_Sound/IOB2: J802.6, U801.11 (IOB2)
/YM2149_Sound/IOB3: J802.8, U801.10 (IOB3)
/YM2149_Sound/IOB4: J802.10, U801.9 (IOB4)
/YM2149_Sound/IOB5: J802.12, U801.8 (IOB5)
/YM2149_Sound/IOB6: J802.14, U801.7 (IOB6)
/YM2149_Sound/IOB7: J802.16, U801.6 (IOB7)
/YM2149_Sound/RING: C806.1, R804.2, R806.2
/YM2149_Sound/TIP: C805.1, R805.2, R807.2
/~IODEV5: J001.57, U703.1, U703.4
/~IODEV6: J001.59, U804.1, U804.2
/~IRQ2: J001.25, J702.1
/~RMEM: J001.72, U703.2, U804.4, U804.13
/~RST: J001.76, U701.34 (~RESET/SYNC), U801.23 (-RST)
/~WMEM: J001.74, U703.5, U804.5, U804.10
GND: C001.2, C701.2, C702.2, C703.2, C704.2, C705.2, C706.2, C707.2, C710.1, C711.1, C801.2, C802.2, C803.2, C804.2, J001.79, J701.1, J801.2, J802.18, J803.1, R701.2, R702.2, R801.2, R802.2, R803.2, U701.12 (VSS), U702.1, U702.3, U702.5, U702.7 (GND), U703.7 (GND), U703.9, U703.10, U703.12, U703.13, U704.10 (GND), U705.1 (OE), U705.2 (D0), U705.10 (GND), U706.1 (OE), U706.2 (D0), U706.10 (GND), U707.1 (A14), U707.14 (GND), U707.20 (~CS), U801.1 (GND), U802.3, U802.4, U802.5, U802.7 (GND), U803.4 (GND), U804.7 (GND)
unnamed: C710.2, U701.39 (XTAL1), Y701.2
unnamed: C711.2, U701.40 (XTAL2), Y701.1
unnamed: C805.2, J803.2
unnamed: C806.2, J803.3
unnamed: J701.2, Q701.1 (E), R702.1
unnamed: J702.2, U701.16 (~INT)
unnamed: J801.1, U801.26 (-SEL)
unnamed: Q701.2 (B), R701.1, U701.36 (COMVID)
unnamed: U702.8, U705.11 (Cp)
unnamed: U702.10, U706.11 (Cp)
unnamed: U801.22 (CLK), U803.5 (CLK)
unnamed: U802.1, U802.9, U804.3
unnamed: U802.2, U802.10, U804.6
unnamed: U802.11, U804.8
unnamed: U802.13, U804.11
VCC: C001.1, C701.1, C702.1, C703.1, C704.1, C705.1, C706.1, C707.1, C801.1, C802.1, C803.1, C804.1, J001.80, J802.17, Q701.3 (C), U701.33 (VCC), U702.14 (VCC), U703.14 (VCC), U704.20 (VCC), U705.20 (VCC), U706.20 (VCC), U707.28 (VCC), U801.28 (BC2), U801.40 (VCC), U802.14 (VCC), U803.8 (VCC), U804.14 (VCC)
