daveho/DIY8bit/Episode1d/HardwareDesign/InterruptAndKeyboard.kicad_pcb

## KiCad design Episode1d/HardwareDesign/InterruptAndKeyboard.kicad_pcb (2021-06-23)

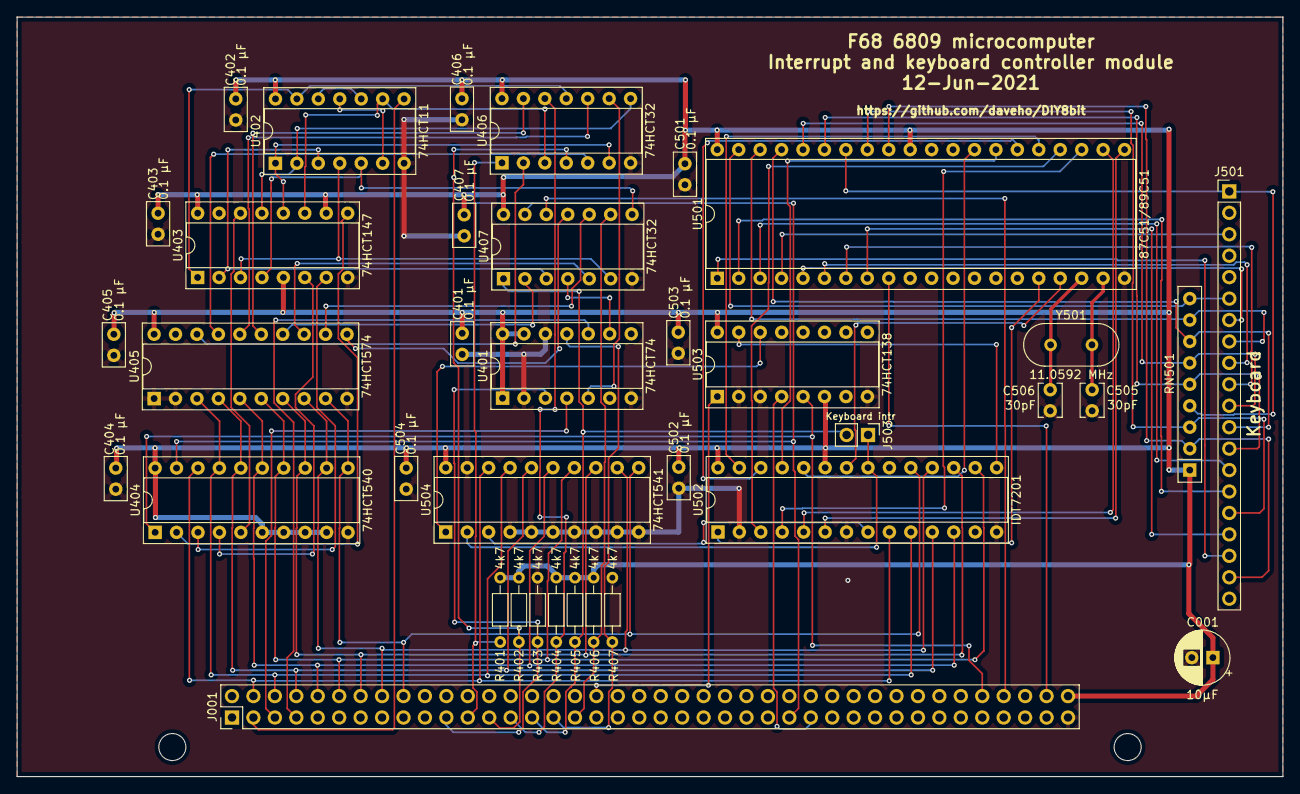
[picture p89: board InterruptAndKeyboard.kicad_pcb from above]

Board: 2 copper layers, 150.0 x 90.0 mm, 37 parts (0 on the bottom side), 81 nets.

Parts:
C001: 10μF; CP_Radial_D6.3mm_P2.50mm
C401, C402, C403, C404, C405, C406, C407, C501, C502, C503, C504: 0.1 μF; C_Disc_D5.0mm_W2.5mm_P2.50mm
C505, C506: 30pF; C_Disc_D3.8mm_W2.6mm_P2.50mm
J001: Conn_02x40_Odd_Even; PinHeader_2x40_P2.54mm_Vertical
J501: Conn_01x20; PinHeader_1x20_P2.54mm_Vertical
J503: Conn_01x02; PinHeader_1x02_P2.54mm_Vertical
R401, R402, R403, R404, R405, R406, R407: 4k7; R_Axial_DIN0204_L3.6mm_D1.6mm_P7.62mm_Horizontal
RN501: R_Network08; R_Array_SIP9
U401: 74HCT74; DIP-14_W7.62mm_Socket
U402: 74HCT11; DIP-14_W7.62mm_Socket
U403: 74HCT147; DIP-16_W7.62mm_Socket
U404: 74HCT540; DIP-20_W7.62mm_Socket
U405: 74HCT574; DIP-20_W7.62mm_Socket
U406, U407: 74HCT32; DIP-14_W7.62mm_Socket
U501: 87C51/89C51; DIP-40_W15.24mm_Socket
U502: IDT7201; DIP-28_W7.62mm_Socket
U503: 74HCT138; DIP-16_W7.62mm_Socket
U504: 74HCT541; DIP-20_W7.62mm_Socket
Y501: 11.0592 MHz; Crystal_HC18-U_Vertical

Connections:
/A0: J001.36, U503.1
/D0: J001.4, U404.18, U502.9, U504.18
/D1: J001.6, U404.17, U405.3, U502.10, U504.17
/D2: J001.8, U404.16, U405.4, U502.11, U504.16
/D3: J001.10, U404.15, U405.5, U502.12, U504.15
/D4: J001.12, U404.14, U405.6, U502.16, U504.14
/D5: J001.14, U404.13, U405.7, U502.17, U504.13
/D6: J001.16, U404.12, U405.8, U502.18, U504.12
/D7: J001.18, U404.11, U405.9, U502.19, U504.11
/IRQ3: J001.21, R403.1, U401.3
/IRQ6: J001.31, R407.1, U401.11
/Interrupts/~IRQ3~: U401.5, U406.9
/Interrupts/~IRQ6~: U401.9, U407.4
/Keyboard/COL0: J501.18, U501.1
/Keyboard/COL1: J501.15, U501.2
/Keyboard/COL2: J501.14, U501.3
/Keyboard/COL3: J501.3, U501.4
/Keyboard/COL4: J501.7, U501.5
/Keyboard/COL5: J501.9, U501.6
/Keyboard/COL6: J501.10, U501.7
/Keyboard/COL7: J501.17, U501.8
/Keyboard/EF: J503.1, U502.21, U504.2
/Keyboard/FF: U502.8, U504.3
/Keyboard/ROW0: J501.6, RN501.9, U501.39
/Keyboard/ROW1: J501.8, RN501.8, U501.38
/Keyboard/ROW2: J501.12, RN501.7, U501.37
/Keyboard/ROW3: J501.11, RN501.6, U501.36
/Keyboard/ROW4: J501.13, RN501.5, U501.35
/Keyboard/ROW5: J501.1, RN501.4, U501.34
/Keyboard/ROW6: J501.16, RN501.3, U501.33
/Keyboard/ROW7: J501.19, RN501.2, U501.32
/Keyboard/SCDAT0: U501.21, U502.6
/Keyboard/SCDAT1: U501.22, U502.5
/Keyboard/SCDAT2: U501.23, U502.4
/Keyboard/SCDAT3: U501.24, U502.3
/Keyboard/SCDAT4: U501.25, U502.27
/Keyboard/SCDAT5: U501.26, U502.26
/Keyboard/SCDAT6: U501.27, U502.25
/Keyboard/SCDAT7: U501.28, U502.24
/Keyboard/~FIFO_CLR: U501.17, U502.22
/Keyboard/~FIFO_WR: U501.16, U502.1
/Keyboard/~RD_CTRL: U503.14, U504.1
/Keyboard/~RD_DATA: U502.15, U503.15
/PC0: J001.5, U401.4
/PC1: J001.7, U401.10
/RST: J001.78, U501.9
/~IODEV3: J001.53, U404.19, U407.13
/~IODEV4: J001.55, U503.4
/~IRQ: J001.3, U402.8
/~IRQ1~: J001.23, R401.2, U406.1
/~IRQ2~: J001.25, R402.2, U406.4
/~IRQ4~: J001.27, R404.2, U406.12
/~IRQ5~: J001.29, J503.2, R405.2, U407.1
/~IRQ7~: J001.33, R406.2, U407.9
/~RMEM~: J001.72, U404.1, U503.5
/~WMEM~: J001.74, U407.12
GND: C001.2, C401.2, C402.2, C403.2, C404.2, C405.2, C406.2, C407.2, C501.2, C502.2, C503.2, C504.2, C505.1, C506.1, J001.79, R403.2, R407.2, U401.2, U401.7, U401.12, U402.7, U403.8, U404.10, U405.1, U405.2, U405.10, U406.7, U407.7, U501.20, U502.2, U502.7, U502.14, U503.2, U503.3, U503.8, U504.4, U504.5, U504.6, U504.7, U504.8, U504.9, U504.10, U504.19
unnamed: C505.2, U501.19, Y501.2
unnamed: C506.2, U501.18, Y501.1
unnamed: U402.1, U403.12, U406.6
unnamed: U402.2, U403.13, U406.8
unnamed: U402.3, U403.2, U407.3
unnamed: U402.4, U403.3, U407.6
unnamed: U402.5, U403.4, U407.8
unnamed: U402.9, U403.11, U406.3
unnamed: U402.10, U402.12
unnamed: U402.6, U402.11
unnamed: U402.13, U403.1, U406.11
unnamed: U403.6, U404.4
unnamed: U403.7, U404.3
unnamed: U403.9, U404.2
unnamed: U403.14, U404.5
unnamed: U405.11, U407.11
unnamed: U405.12, U407.10
unnamed: U405.13, U407.5
unnamed: U405.14, U407.2
unnamed: U405.15, U406.13
unnamed: U405.16, U406.10
unnamed: U405.17, U406.5
unnamed: U405.18, U406.2
VCC: C001.1, C401.1, C402.1, C403.1, C404.1, C405.1, C406.1, C407.1, C501.1, C502.1, C503.1, C504.1, J001.80, R401.1, R402.1, R404.1, R405.1, R406.1, RN501.1, U401.1, U401.13, U401.14, U402.14, U403.5, U403.10, U403.16, U404.6, U404.7, U404.8, U404.9, U404.20, U405.20, U406.14, U407.14, U501.31, U501.40, U502.23, U502.28, U503.6, U503.16, U504.20
