daveho/DIY8bit/Episode1d/HardwareDesign/MemoryAndPeripherals.kicad_pcb

## KiCad design Episode1d/HardwareDesign/MemoryAndPeripherals.kicad_pcb (2021-08-18)

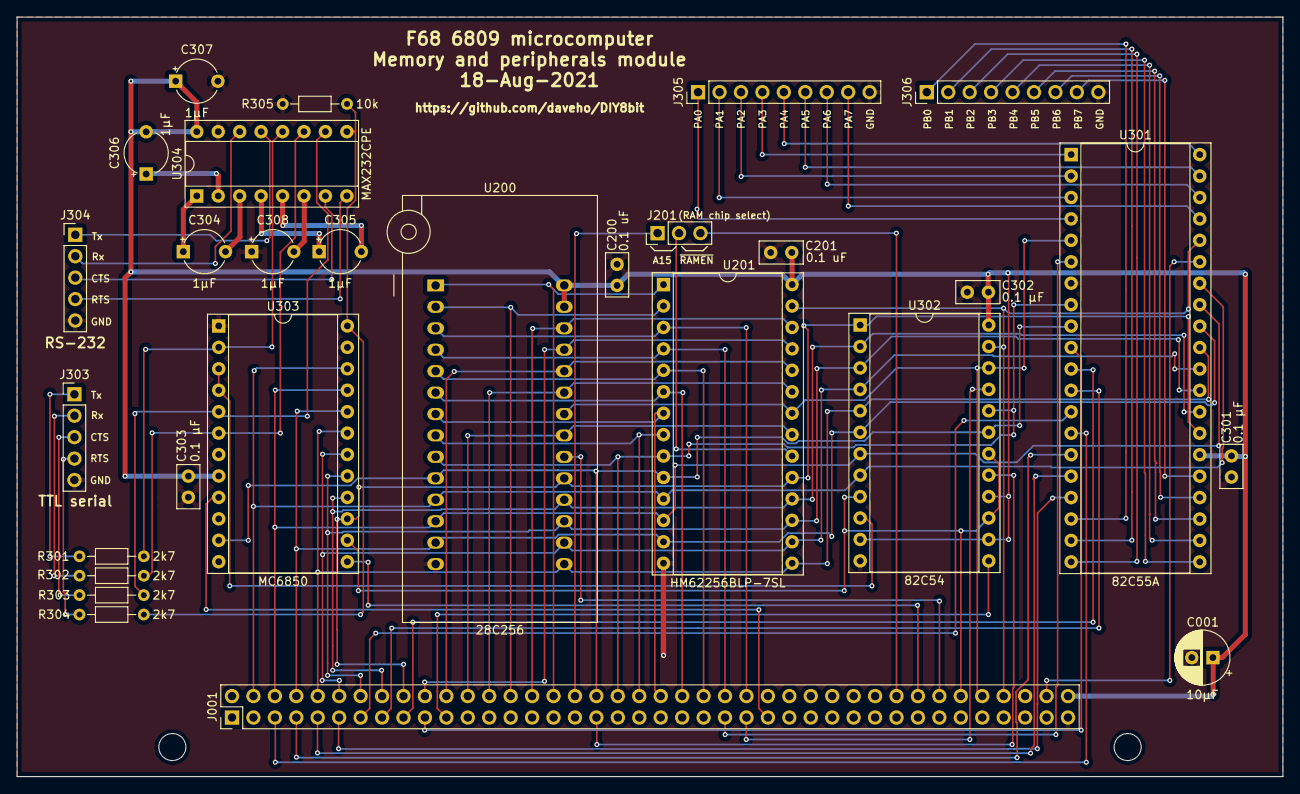
[picture p90: board MemoryAndPeripherals.kicad_pcb from above]

Board: 2 copper layers, 150.0 x 90.0 mm, 28 parts (0 on the bottom side), 82 nets.

Parts:
C001: 10μF; CP_Radial_D6.3mm_P2.50mm
C200, C201: 0.1 uF; C_Disc_D5.0mm_W2.5mm_P2.50mm
C301, C302, C303: 0.1 μF; C_Disc_D5.0mm_W2.5mm_P2.50mm
C304, C305, C306, C307, C308: 1μF; CP_Radial_Tantal_D5.0mm_P5.00mm
J001: Conn_02x40_Odd_Even; PinHeader_2x40_P2.54mm_Vertical
J201: Conn_01x03; PinHeader_1x03_P2.54mm_Vertical
J303, J304: Conn_01x05; PinHeader_1x05_P2.54mm_Vertical
J305, J306: Conn_01x09; PinHeader_1x09_P2.54mm_Vertical
R301, R302, R303, R304: 2k7; R_Axial_DIN0204_L3.6mm_D1.6mm_P7.62mm_Horizontal
R305: 10k; R_Axial_DIN0204_L3.6mm_D1.6mm_P7.62mm_Horizontal
U200: 28C256; DIP_Socket-28_W11.9_W12.7_W15.24_W17.78_W18.5_3M_228-1277-0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
U201: HM62256BLP-7SL; DIP-28_W15.24mm_Socket
U301: 82C55A; DIP-40_W15.24mm_Socket
U302: 82C54; DIP-24_W15.24mm_Socket
U303: MC6850; DIP-24_W15.24mm_Socket
U304: MAX232CPE; DIP-16_W7.62mm_Socket

Connections:
/A0: J001.36, U200.10, U201.10, U301.9, U302.19, U303.11
/A1: J001.38, U200.9, U201.9, U301.8, U302.20
/A2: J001.40, U200.8, U201.8
/A3: J001.42, U200.7, U201.7
/A4: J001.44, U200.6, U201.6
/A5: J001.46, U200.5, U201.5
/A6: J001.48, U200.4, U201.4
/A7: J001.50, U200.3, U201.3
/A8: J001.20, U200.25, U201.25
/A9: J001.22, U200.24, U201.24
/A10: J001.24, U200.21, U201.21
/A11: J001.26, U200.23, U201.23
/A12: J001.28, U200.2, U201.2
/A13: J001.30, U200.26, U201.26
/A14: J001.32, U200.1, U201.1
/A15: J001.34, J201.1
/CorePeriphs/-CTS: R304.2, R305.1, U303.24, U304.9
/CorePeriphs/-RTS: R303.2, U303.5, U304.10
/CorePeriphs/Ext_CTS: J304.3, U304.7
/CorePeriphs/Ext_RTS: J304.4, U304.8
/CorePeriphs/Ext_RxD: J304.2, U304.14
/CorePeriphs/Ext_TxD: J304.1, U304.13
/CorePeriphs/PA0: J305.1, U301.4
/CorePeriphs/PA1: J305.2, U301.3
/CorePeriphs/PA2: J305.3, U301.2
/CorePeriphs/PA3: J305.4, U301.1
/CorePeriphs/PA4: J305.5, U301.40
/CorePeriphs/PA5: J305.6, U301.39
/CorePeriphs/PA6: J305.7, U301.38
/CorePeriphs/PA7: J305.8, U301.37
/CorePeriphs/PB0: J306.1, U301.18
/CorePeriphs/PB1: J306.2, U301.19
/CorePeriphs/PB2: J306.3, U301.20
/CorePeriphs/PB3: J306.4, U301.21
/CorePeriphs/PB4: J306.5, U301.22
/CorePeriphs/PB5: J306.6, U301.23
/CorePeriphs/PB6: J306.7, U301.24
/CorePeriphs/PB7: J306.8, U301.25
/CorePeriphs/RxD: R301.2, U303.2, U304.12
/CorePeriphs/TxD: R302.2, U303.6, U304.11
/D0: J001.4, U200.11, U201.11, U301.34, U302.8, U303.22
/D1: J001.6, U200.12, U201.12, U301.33, U302.7, U303.21
/D2: J001.8, U200.13, U201.13, U301.32, U302.6, U303.20
/D3: J001.10, U200.15, U201.15, U301.31, U302.5, U303.19
/D4: J001.12, U200.16, U201.16, U301.30, U302.4, U303.18
/D5: J001.14, U200.17, U201.17, U301.29, U302.3, U303.17
/D6: J001.16, U200.18, U201.18, U301.28, U302.2, U303.16
/D7: J001.18, U200.19, U201.19, U301.27, U302.1, U303.15
/E: J001.70, U302.9, U302.15, U302.18, U303.14
/IRQ3: J001.21, U302.13
/PC0: J001.5, U301.14
/PC1: J001.7, U301.15
/PC2: J001.9, U301.16
/PC3: J001.11, U301.17
/PC4: J001.13, U301.13
/PC5: J001.15, U301.12
/PC6: J001.17, U301.11
/PC7: J001.19, U301.10
/RST: J001.78, U301.35
/R~W~: J001.66, U303.13
/TCOUNT2: J001.35, U302.17
/~IODEV0: J001.47, U301.6
/~IODEV1: J001.49, U302.21
/~IODEV2: J001.51, U303.9
/~RAMEN~: J001.64, J201.3
/~RMEM~: J001.72, U200.22, U201.22, U301.5, U302.22
/~ROMEN~: J001.68, U200.20
/~WMEM~: J001.74, U201.27, U301.36, U302.23
GND: C001.2, C200.2, C201.2, C301.2, C302.2, C303.2, C307.2, C308.1, J001.79, J303.5, J304.5, J305.9, J306.9, R305.2, U200.14, U201.14, U301.7, U302.12, U303.1, U303.23, U304.15
unnamed: C304.1, U304.1
unnamed: C304.2, U304.3
unnamed: C305.1, U304.4
unnamed: C305.2, U304.5
unnamed: C306.1, U304.2
unnamed: C308.2, U304.6
unnamed: J201.2, U201.20
unnamed: J303.1, R301.1
unnamed: J303.2, R302.1
unnamed: J303.3, R303.1
unnamed: J303.4, R304.1
unnamed: U302.10, U303.3, U303.4
VCC: C001.1, C200.1, C201.1, C301.1, C302.1, C303.1, C306.2, C307.1, J001.80, U200.27, U200.28, U201.28, U301.26, U302.11, U302.14, U302.16, U302.24, U303.8, U303.10, U303.12, U304.16
