daveho/DIY8bit/Episode0d/CircuitWithPeriphs/CorePeriphs.sch

## KiCad design Episode0d/CircuitWithPeriphs/CorePeriphs.sch (2020-01-04)

Schematic: CorePeriphs.sch

Parts:
C301, C302, C303: C
J303: Conn_01x05
R301, R302, R303, R304: 2k7
U301: 82C55A; DIP-40_W15.24mm
U302: 82C54; DIP-24_W15.24mm
U303: MC6850; MODULE

Notes on the sheet:
core peripheral devices: GPIO, timer, serial
Connections to FT232RL breakout
CTS
RTS
GND
THIS SCHEMATIC IS WRONG! See the schematic in Episode0f for correct way to interface 6850 ACIA and FT232RL breakout
