daveho/DIY8bit/FPGADisplayController/sync.v

// Sync module, based on Sync.pld from the HW_VGA project

module sync( // Inputs
             input nrst,
             input clk,
             input hBeginPulse,
             input hEndPulse,
             input vBeginPulse,
             input vEndPulse,
             input hCountEnd,
             input vCountZero,
             input hVisEnd,
             input vVisEnd,
             input vCountEnd,
             input vEndActive,
             // Outputs
             output hSync,
             output vSync,
             output hVis,
             output vVis,
             output nVis,
             output vActive );

  // registers for registered outputs
  reg hSyncReg, vSyncReg, hVisReg, vVisReg, vActiveReg;

  always @( posedge clk ) begin
    if ( nrst == 1'b0 ) begin
      // in reset: hSync and vSync are high,
      // hVis is true, vVis is false, vActive is false
      hSyncReg <= 1'b1;
      vSyncReg <= 1'b1;
      hVisReg <= 1'b1;
      vVisReg <= 1'b0;
      vActiveReg <= 1'b0;
    end else begin
      // not in reset

      // update hSyncReg if needed
      if ( hBeginPulse ) begin
        // begin hsync pulse
        hSyncReg <= 1'b0;
      end else if ( hEndPulse ) begin
        // end hsync pulse
        hSyncReg <= 1'b1;
      end

      // update vSyncReg if needed
      if ( vBeginPulse ) begin
        // begin vsync pulse
        vSyncReg <= 1'b0;
      end else if ( vEndPulse ) begin
        // end vsync pulse
        vSyncReg <= 1'b1;
      end

      // update hVisReg if needed
      if ( hCountEnd ) begin
        // beginning of horizontal visible region
        hVisReg <= 1'b1;
      end else if ( hVisEnd ) begin
        // end of horizontal visible region
        hVisReg <= 1'b0;
      end

      // update vVisReg if needed
      if ( hCountEnd & vCountZero ) begin
        // beginning of vertical visible region;
        // note that because the vertical count is incremented before
        // the end of the scanline, vcount is 0 when vertical visibility
        // begins, not 524
        vVisReg <= 1'b1;
      end else if ( hCountEnd & vVisEnd ) begin
        // end of vertical visible region
        vVisReg <= 1'b0;
      end

      // update vActive if needed
      if ( hCountEnd & vCountEnd ) begin
        // Begin vertical activity. Note that this happens
        // at the end of the next-to-last scanline of the frame.
        // This allows readout activity to start on the last
        // scanline of the frame, which preceeds the first
        // visible scanline (in the next frame.)
        vActiveReg <= 1'b1;
      end else if ( vEndActive & hCountEnd ) begin
        // We're at the end of the last scanline of vertical
        // activity, so vActive is turned off here.
        vActiveReg = 1'b0;
      end
    end
  end

  // drive register outputs to corresponding module outputs
  assign hSync = hSyncReg;
  assign vSync = vSyncReg;
  assign hVis = hVisReg;
  assign vVis = vVisReg;

  // Active-low visibility signal:
  // if either hVis or vVis is not asserted,
  // then nVis is high (not asserted)
  assign nVis = ~hVis | ~vVis;

  assign vActive = vActiveReg;

endmodule
