daveho/DIY8bit/LatestVerilog/Experiment01/ArduinoSketch/vga_font.ino

// IBM DOS ISO8 VGA font:
// See: https://int10h.org/oldschool-pc-fonts/fontlist/font?ibm_dos_iso8

const PROGMEM uint8_t font_data[] = {
  // character 0
  0x00, 0x00, 0x00, 0x00, 0x00, 0x00, 0x00, 0x00, 0x00, 0x00, 0x00, 0x00, 0x00, 0x00, 0x00, 0x00,
  // character 1
  0x00, 0x00, 0x7C, 0x82, 0x82, 0xAA, 0x82, 0x82, 0xBA, 0x92, 0x82, 0x7C, 0x00, 0x00, 0x00, 0x00,
  // character 2
  0x00, 0x00, 0x7C, 0xFE, 0xFE, 0xD6, 0xFE, 0xFE, 0xC6, 0xEE, 0xFE, 0x7C, 0x00, 0x00, 0x00, 0x00,
  // character 3
  0x00, 0x00, 0x00, 0x00, 0x00, 0x6C, 0xFE, 0xFE, 0x7C, 0x38, 0x10, 0x00, 0x00, 0x00, 0x00, 0x00,
  // character 4
  0x00, 0x00, 0x00, 0x00, 0x10, 0x38, 0x7C, 0xFE, 0x7C, 0x38, 0x10, 0x00, 0x00, 0x00, 0x00, 0x00,
  // character 5
  0x00, 0x00, 0x00, 0x00, 0x38, 0x38, 0x38, 0xEE, 0xEE, 0xEE, 0x10, 0x38, 0x00, 0x00, 0x00, 0x00,
  // character 6
  0x00, 0x00, 0x00, 0x00, 0x10, 0x38, 0x7C, 0xFE, 0xFE, 0x54, 0x10, 0x38, 0x00, 0x00, 0x00, 0x00,
  // character 7
  0x00, 0x00, 0x00, 0x00, 0x00, 0x00, 0x18, 0x3C, 0x3C, 0x18, 0x00, 0x00, 0x00, 0x00, 0x00, 0x00,
  // character 8
  0xFF, 0xFF, 0xFF, 0xFF, 0xFF, 0xFF, 0xE7, 0xC3, 0xC3, 0xE7, 0xFF, 0xFF, 0xFF, 0xFF, 0xFF, 0xFF,
  // character 9
  0x00, 0x00, 0x00, 0x00, 0x00, 0x3C, 0x66, 0x42, 0x42, 0x66, 0x3C, 0x00, 0x00, 0x00, 0x00, 0x00,
  // character 10
  0xFF, 0xFF, 0xFF, 0xFF, 0xFF, 0xC3, 0x99, 0xBD, 0xBD, 0x99, 0xC3, 0xFF, 0xFF, 0xFF, 0xFF, 0xFF,
  // character 11
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
  // character 249
  0x00, 0x00, 0x00, 0x00, 0x00, 0x00, 0x00, 0x30, 0x30, 0x00, 0x00, 0x00, 0x00, 0x00, 0x00, 0x00,
  // character 250
  0x00, 0x00, 0x00, 0x00, 0x00, 0x00, 0x00, 0x00, 0x30, 0x00, 0x00, 0x00, 0x00, 0x00, 0x00, 0x00,
  // character 251
  0x00, 0x0E, 0x08, 0x08, 0x08, 0x08, 0x08, 0x08, 0xC8, 0x28, 0x18, 0x08, 0x00, 0x00, 0x00, 0x00,
  // character 252
  0x00, 0xB8, 0x44, 0x44, 0x44, 0x44, 0x44, 0x00, 0x00, 0x00, 0x00, 0x00, 0x00, 0x00, 0x00, 0x00,
  // character 253
  0x00, 0x60, 0x90, 0x10, 0x20, 0x40, 0xF0, 0x00, 0x00, 0x00, 0x00, 0x00, 0x00, 0x00, 0x00, 0x00,
  // character 254
  0x00, 0x00, 0x00, 0x00, 0x7C, 0x7C, 0x7C, 0x7C, 0x7C, 0x7C, 0x7C, 0x00, 0x00, 0x00, 0x00, 0x00,
  // character 255
  0x00, 0x00, 0x00, 0x00, 0x00, 0x00, 0x00, 0x00, 0x00, 0x00, 0x00, 0x00, 0x00, 0x00, 0x00, 0x00,
};
